lukacslacko/wonkycube/designs/pentagonal-prism-v1/plate-maps.html

# Wonky pentagonal prism — 60° — plate maps

Millimetres, 100% scale. Geometry only. Mark every piece with its full ID.

## C-01



## V-01



## H-01



## K-01



## V-face-down-01



## H-face-down-01



## K-radial-down-01



## core-01



## alternate-cores-01



## fit-coupons-01



## stand-01
