lukacslacko/wonkycube/designs/rhombic-dodecahedron-v5.1/NEIGHBORS.md

# Solved neighbors

T = threefold screwed center (8 copies), S = fourfold screwed center (6 copies), P = floating petal (24 copies). Every plastic copy within a type is identical; colored inlays identify the solved placement.

Each petal borders one T and one S center and straddles two rhombic faces. A T center has three neighboring petals; an S center has four. Neighbors here share an exterior seam; contact only at a tip is excluded.

| Piece | Seam neighbors |
|---|---|
| T01 | P01, P02, P03 |
| T02 | P04, P05, P06 |
| T03 | P07, P08, P09 |
| T04 | P10, P11, P12 |
| T05 | P13, P14, P15 |
| T06 | P16, P17, P18 |
| T07 | P19, P20, P21 |
| T08 | P22, P23, P24 |
| S01 | P01, P04, P07, P10 |
| S02 | P13, P16, P19, P22 |
| S03 | P02, P05, P14, P17 |
| S04 | P08, P11, P20, P23 |
| S05 | P03, P09, P15, P21 |
| S06 | P06, P12, P18, P24 |
| P01 | T01, S01 |
| P02 | T01, S03 |
| P03 | T01, S05 |
| P04 | T02, S01 |
| P05 | T02, S03 |
| P06 | T02, S06 |
| P07 | T03, S01 |
| P08 | T03, S04 |
| P09 | T03, S05 |
| P10 | T04, S01 |
| P11 | T04, S04 |
| P12 | T04, S06 |
| P13 | T05, S02 |
| P14 | T05, S03 |
| P15 | T05, S05 |
| P16 | T06, S02 |
| P17 | T06, S03 |
| P18 | T06, S06 |
| P19 | T07, S02 |
| P20 | T07, S04 |
| P21 | T07, S05 |
| P22 | T08, S02 |
| P23 | T08, S04 |
| P24 | T08, S06 |

## Axis labels

Coordinates use the six fourfold vertices as X/Y/Z. Threefold directions are listed as proportional vectors.

| Center | Direction | Ordinary turn |
|---|---|---|
| T01 | -1, -1, -1 | 120° |
| T02 | -1, -1, 1 | 120° |
| T03 | -1, 1, -1 | 120° |
| T04 | -1, 1, 1 | 120° |
| T05 | 1, -1, -1 | 120° |
| T06 | 1, -1, 1 | 120° |
| T07 | 1, 1, -1 | 120° |
| T08 | 1, 1, 1 | 120° |
| S01 | -1, 0, 0 | 90° |
| S02 | 1, 0, 0 | 90° |
| S03 | 0, -1, 0 | 90° |
| S04 | 0, 1, 0 | 90° |
| S05 | 0, 0, -1 | 90° |
| S06 | 0, 0, 1 | 90° |
