lukacslacko/wonkycube/designs/curvy-copter-cuboctahedron-v3.2/NEIGHBORS.md

# Solved neighbors

C = screwed center; P = petal; K = floating corner. Every copy in a family is identical. The plate names and painting map use these labels.

| Piece | Exterior seam neighbors |
|---|---|
| C01 | P01, P04, P05, P12 |
| C02 | P01, P02, P06, P07 |
| C03 | P02, P03, P08, P09 |
| C04 | P03, P04, P10, P11 |
| C05 | P05, P06, P13, P14 |
| C06 | P07, P08, P15, P16 |
| C07 | P09, P10, P17, P18 |
| C08 | P11, P12, P19, P20 |
| C09 | P13, P20, P21, P24 |
| C10 | P14, P15, P21, P22 |
| C11 | P16, P17, P22, P23 |
| C12 | P18, P19, P23, P24 |
| K01 | P01, P05, P06 |
| K02 | P02, P07, P08 |
| K03 | P03, P09, P10 |
| K04 | P04, P11, P12 |
| K05 | P13, P14, P21 |
| K06 | P15, P16, P22 |
| K07 | P17, P18, P23 |
| K08 | P19, P20, P24 |
| P01 | C01, C02, K01 |
| P02 | C02, C03, K02 |
| P03 | C03, C04, K03 |
| P04 | C01, C04, K04 |
| P05 | C01, C05, K01 |
| P06 | C02, C05, K01 |
| P07 | C02, C06, K02 |
| P08 | C03, C06, K02 |
| P09 | C03, C07, K03 |
| P10 | C04, C07, K03 |
| P11 | C04, C08, K04 |
| P12 | C01, C08, K04 |
| P13 | C05, C09, K05 |
| P14 | C05, C10, K05 |
| P15 | C06, C10, K06 |
| P16 | C06, C11, K06 |
| P17 | C07, C11, K07 |
| P18 | C07, C12, K07 |
| P19 | C08, C12, K08 |
| P20 | C08, C09, K08 |
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

| Center | Axis (proportional coordinates) |
|---|---|
| C01 | -1, 0, 1 |
| C02 | 0, -1, 1 |
| C03 | 1, 0, 1 |
| C04 | 0, 1, 1 |
| C05 | -1, -1, 0 |
| C06 | 1, -1, 0 |
| C07 | 1, 1, 0 |
| C08 | -1, 1, 0 |
| C09 | -1, 0, -1 |
| C10 | 0, -1, -1 |
| C11 | 1, 0, -1 |
| C12 | 0, 1, -1 |
