lukacslacko/wonkycube/designs/redi-v4.3/NEIGHBORS.md

# Solved neighbors — compact Redi v4.3

Use these **v4.2 Redi IDs**, not the 65° prototype’s edge ordering. Write each full ID on a sheltered inside patch, away from sliding surfaces. Tick each box after printing and marking.

Neighbors share an exterior seam in the solved state. Point contacts are excluded; the list is not clockwise. For orientation, use the named solved 3MF and the identification image. The core supports all eight C pieces.

| Marked | Piece | Solved seam neighbors |
|---|---|---|
| ☐ | C01 | E01, E02, E05 |
| ☐ | C02 | E01, E03, E06 |
| ☐ | C03 | E02, E04, E07 |
| ☐ | C04 | E03, E04, E08 |
| ☐ | C05 | E05, E09, E10 |
| ☐ | C06 | E06, E09, E11 |
| ☐ | C07 | E07, E10, E12 |
| ☐ | C08 | E08, E11, E12 |
| ☐ | E01 | C01, C02 |
| ☐ | E02 | C01, C03 |
| ☐ | E03 | C02, C04 |
| ☐ | E04 | C03, C04 |
| ☐ | E05 | C01, C05 |
| ☐ | E06 | C02, C06 |
| ☐ | E07 | C03, C07 |
| ☐ | E08 | C04, C08 |
| ☐ | E09 | C05, C06 |
| ☐ | E10 | C05, C07 |
| ☐ | E11 | C06, C08 |
| ☐ | E12 | C07, C08 |

For each E piece, its two C neighbors identify the two ends. Match the ends against the solved model before adding optional end labels. Assembly order is **E → C**; see [ASSEMBLY.md](ASSEMBLY.md).
