lukacslacko/wonkycube/designs/redi-v4.3/plate-maps.html

# Compact Redi v4.3 print plates

Edges point inward toward −Z, with their inner feet downward. These are geometry-only plates; choose slicer settings yourself.

## C-01



## E-01



## core-01



## fit-coupons-01



## optional-01



## optional-core-5.50-01



## optional-core-5.70-01
