lukacslacko/wonkycube/designs/conical-3x3-v1.1/images/catalog-E.png

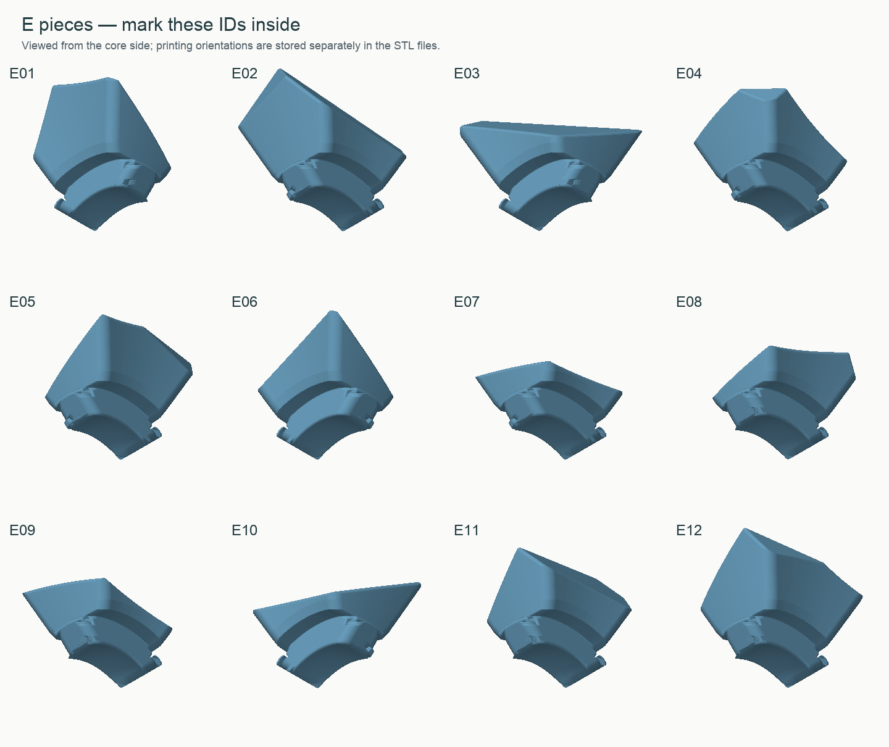
designs/conical-3x3-v1.1/images/catalog-E.png
