lukacslacko/wonkycube/designs/curvy-copter-cuboctahedron-v3.2/images/internal-pieces.png

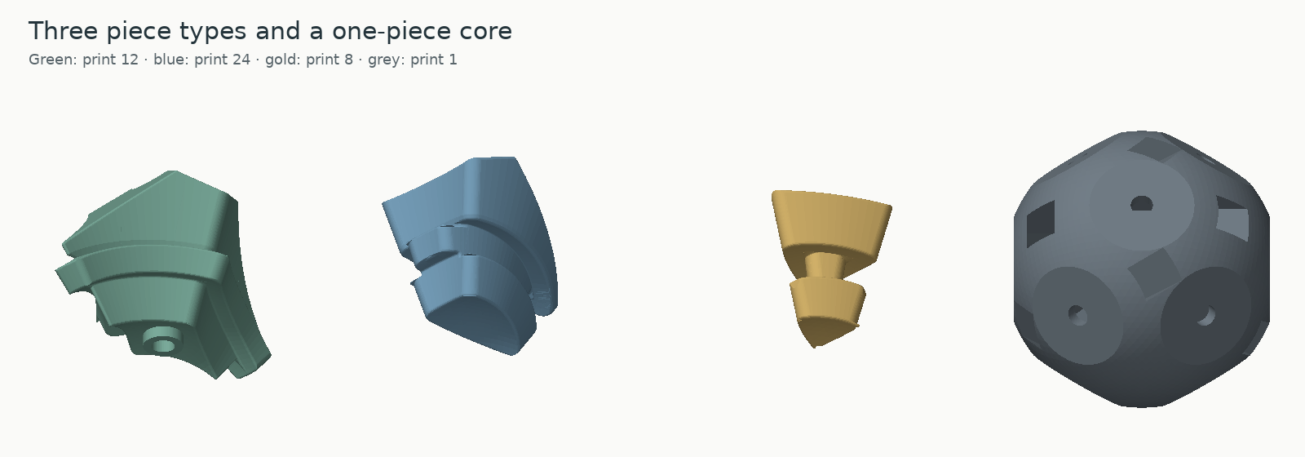
designs/curvy-copter-cuboctahedron-v3.2/images/internal-pieces.png
