lukacslacko/wonkycube/designs/curvy-copter-cuboctahedron-v3.2/images/spherical-profile.png

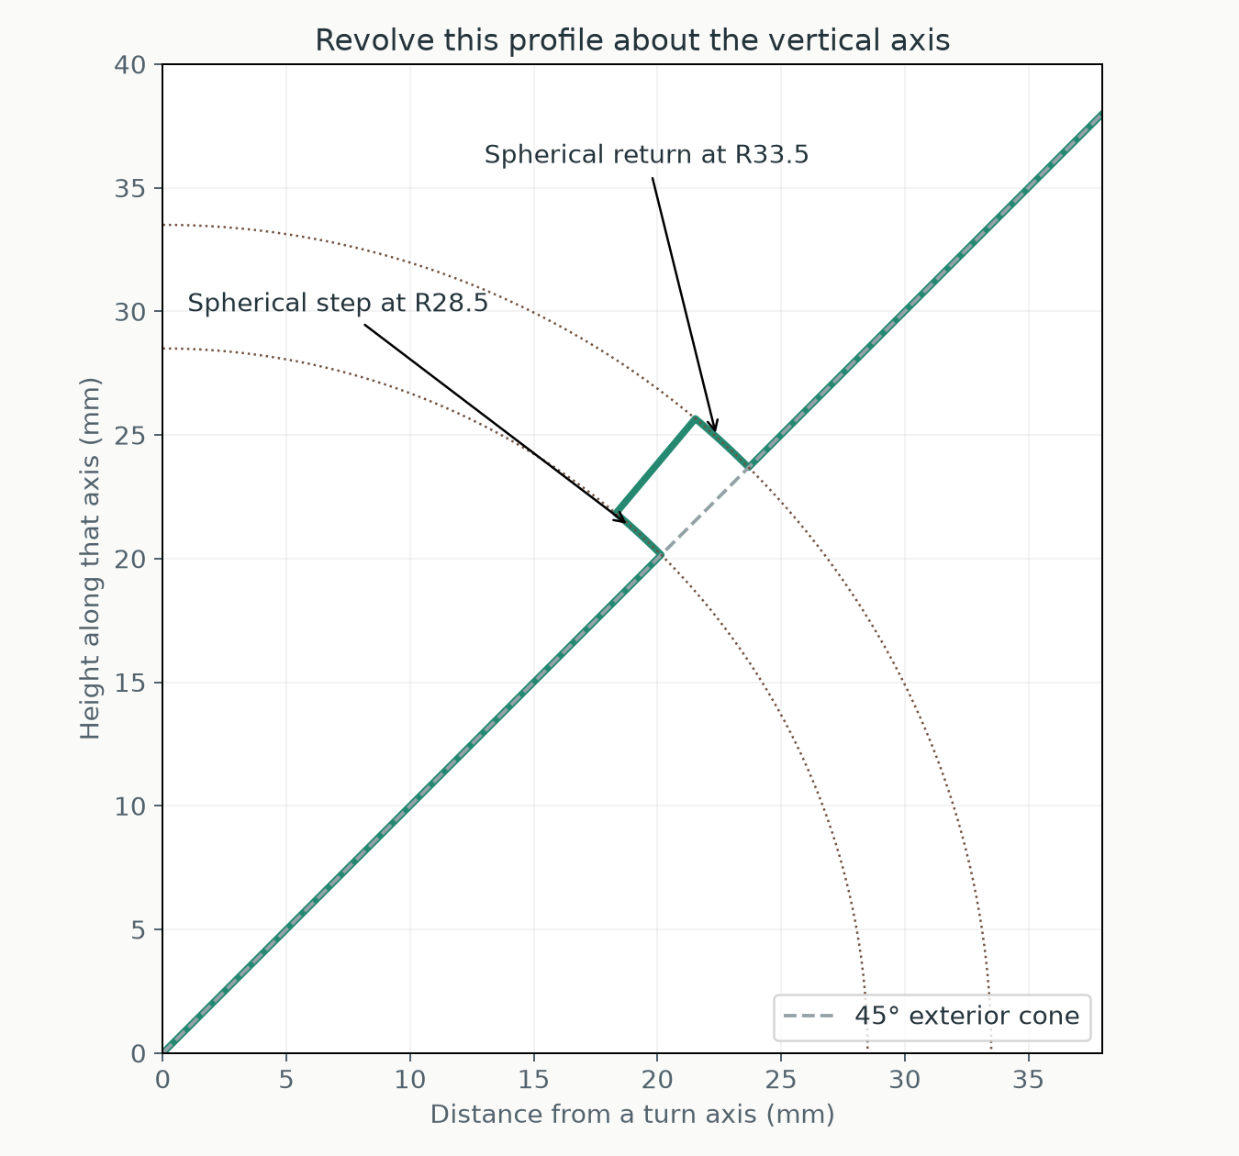
designs/curvy-copter-cuboctahedron-v3.2/images/spherical-profile.png
