lukacslacko/wonkycube/designs/redi-v4.3/images/piece-identification.png

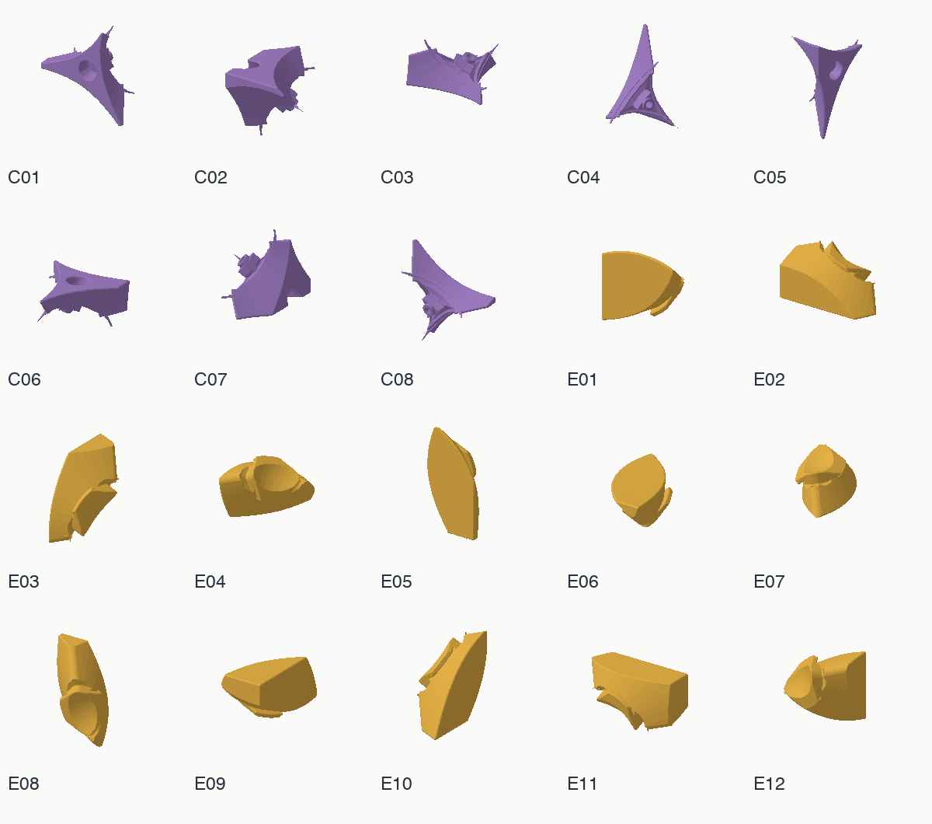
designs/redi-v4.3/images/piece-identification.png
