lukacslacko/wonkycube/designs/skewb-v1.1/images/core-identification.png

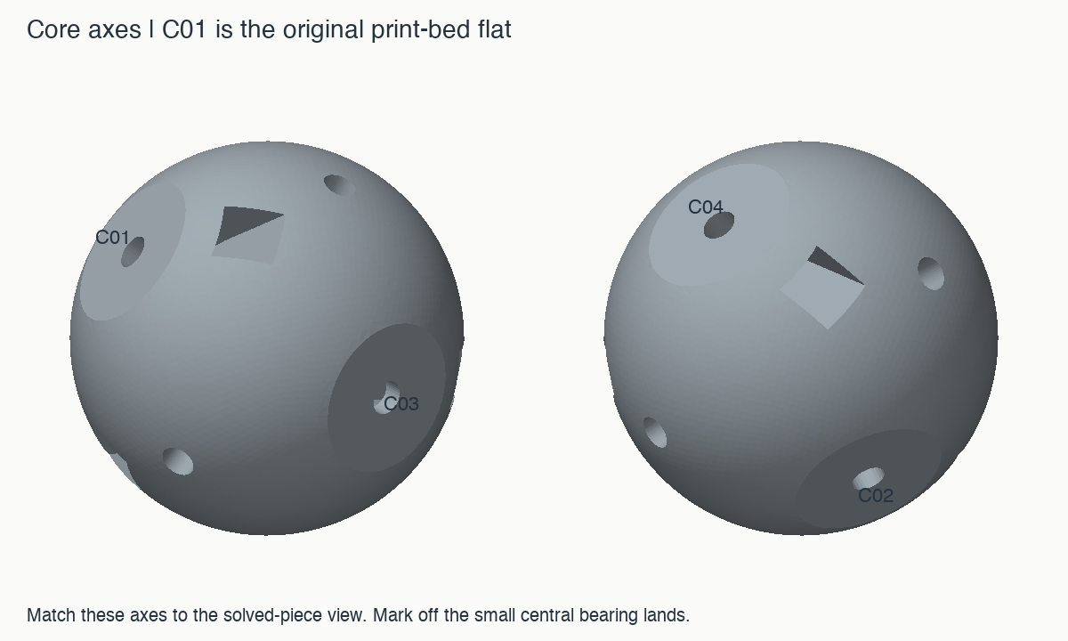
designs/skewb-v1.1/images/core-identification.png
