lukacslacko/wonkycube/designs/skewb-v1.1/images/mechanism.png

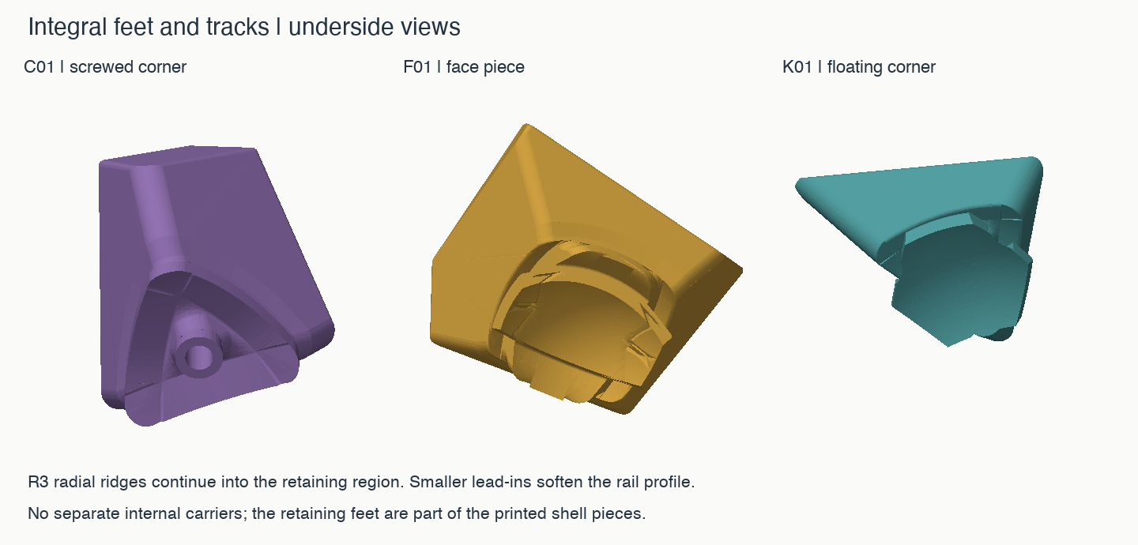
designs/skewb-v1.1/images/mechanism.png
