lukacslacko/wonkycube/designs/triangular-prism-v1/images/catalog-C.png

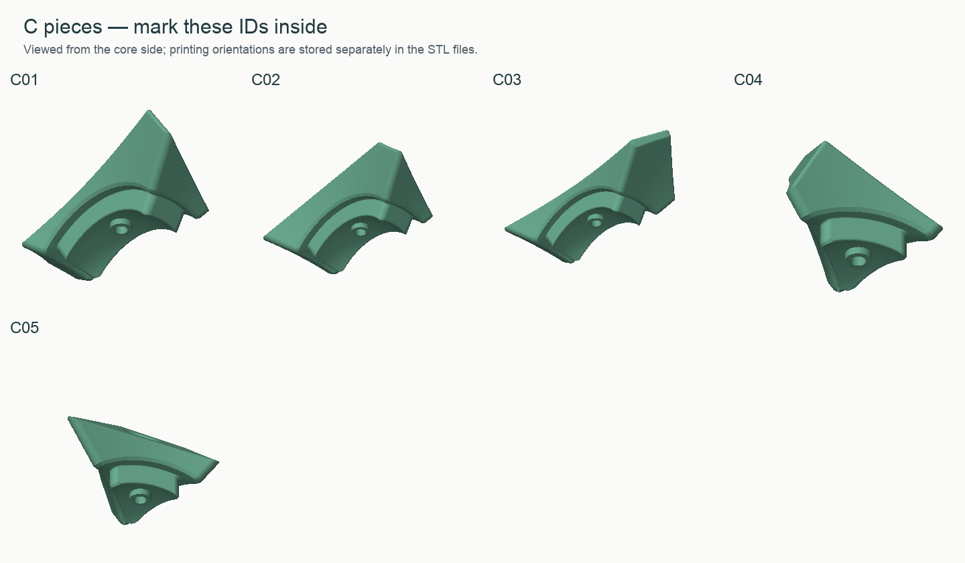
designs/triangular-prism-v1/images/catalog-C.png
