lukacslacko/wonkycube/designs/triangular-prism-v1/images/catalog-H.png

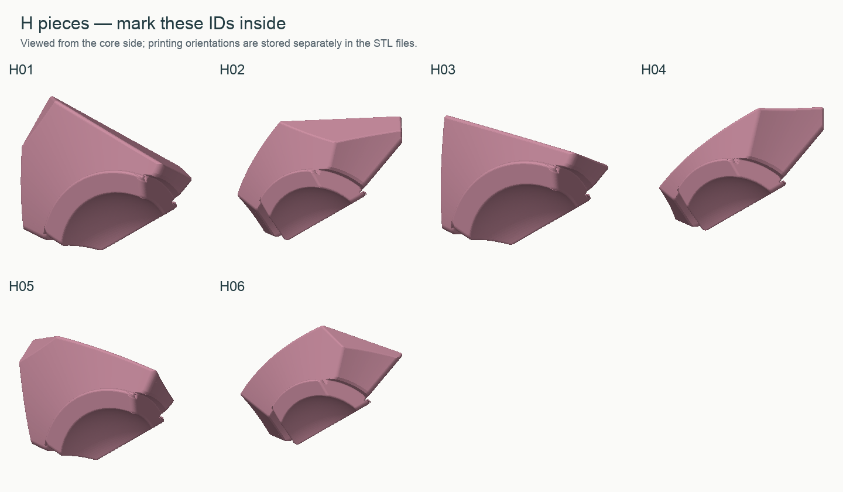
designs/triangular-prism-v1/images/catalog-H.png
