lukacslacko/wonkycube/designs/triangular-prism-v1/images/catalog-K.png

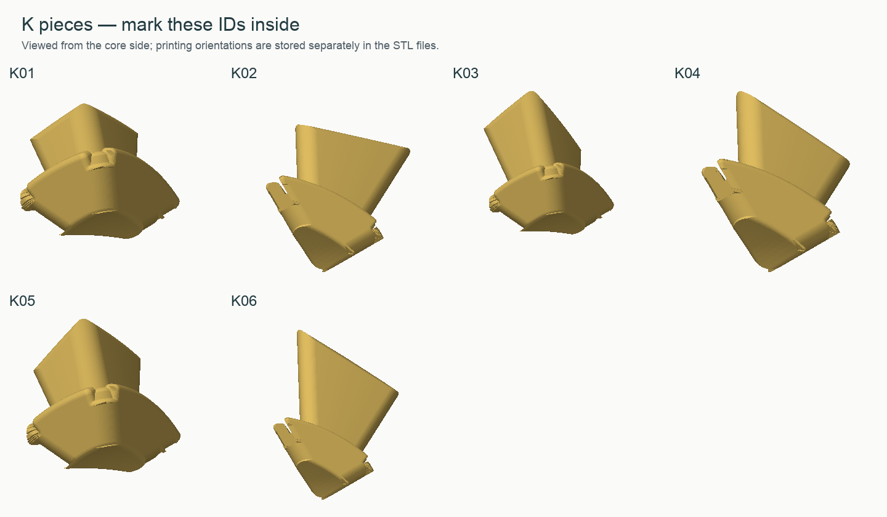
designs/triangular-prism-v1/images/catalog-K.png
