lukacslacko/wonkycube/designs/triangular-prism-v1/images/catalog-V.png

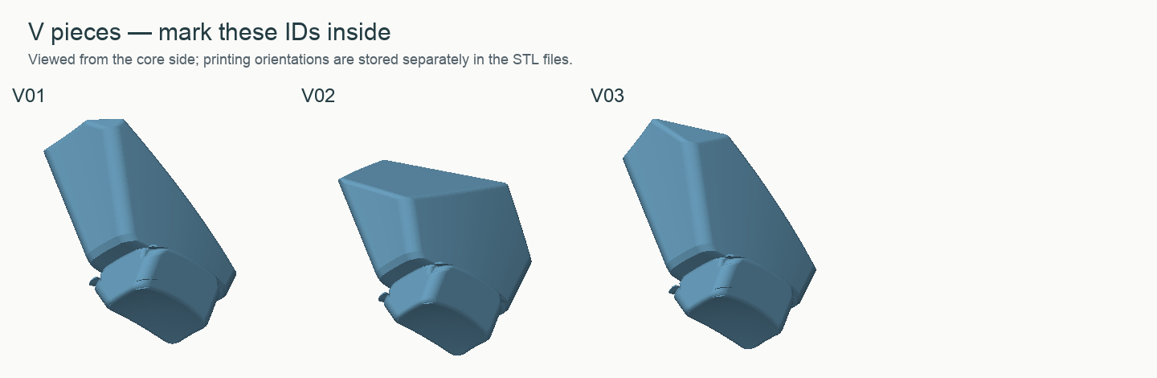
designs/triangular-prism-v1/images/catalog-V.png
