lukacslacko/wonkycube/designs/triangular-prism-v1/images/exploded.png

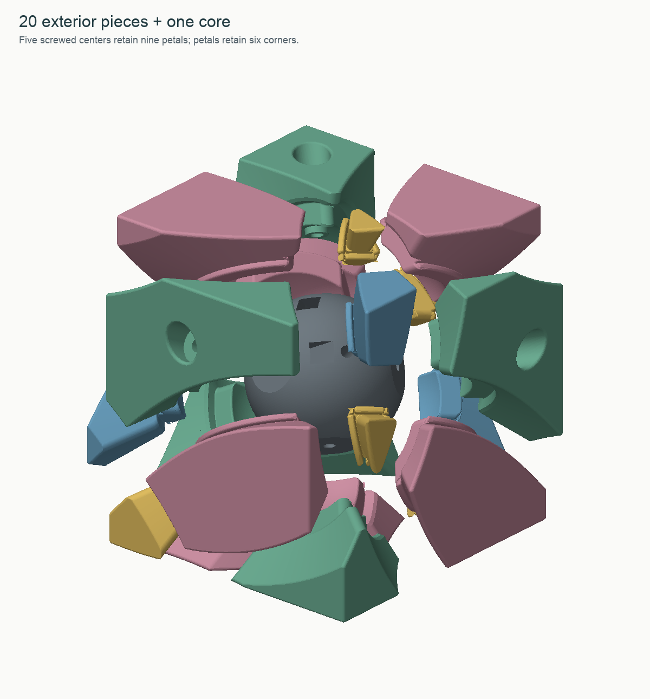
designs/triangular-prism-v1/images/exploded.png
