lukacslacko/wonkycube/designs/triangular-prism-v1/images/screw-stack-section.png

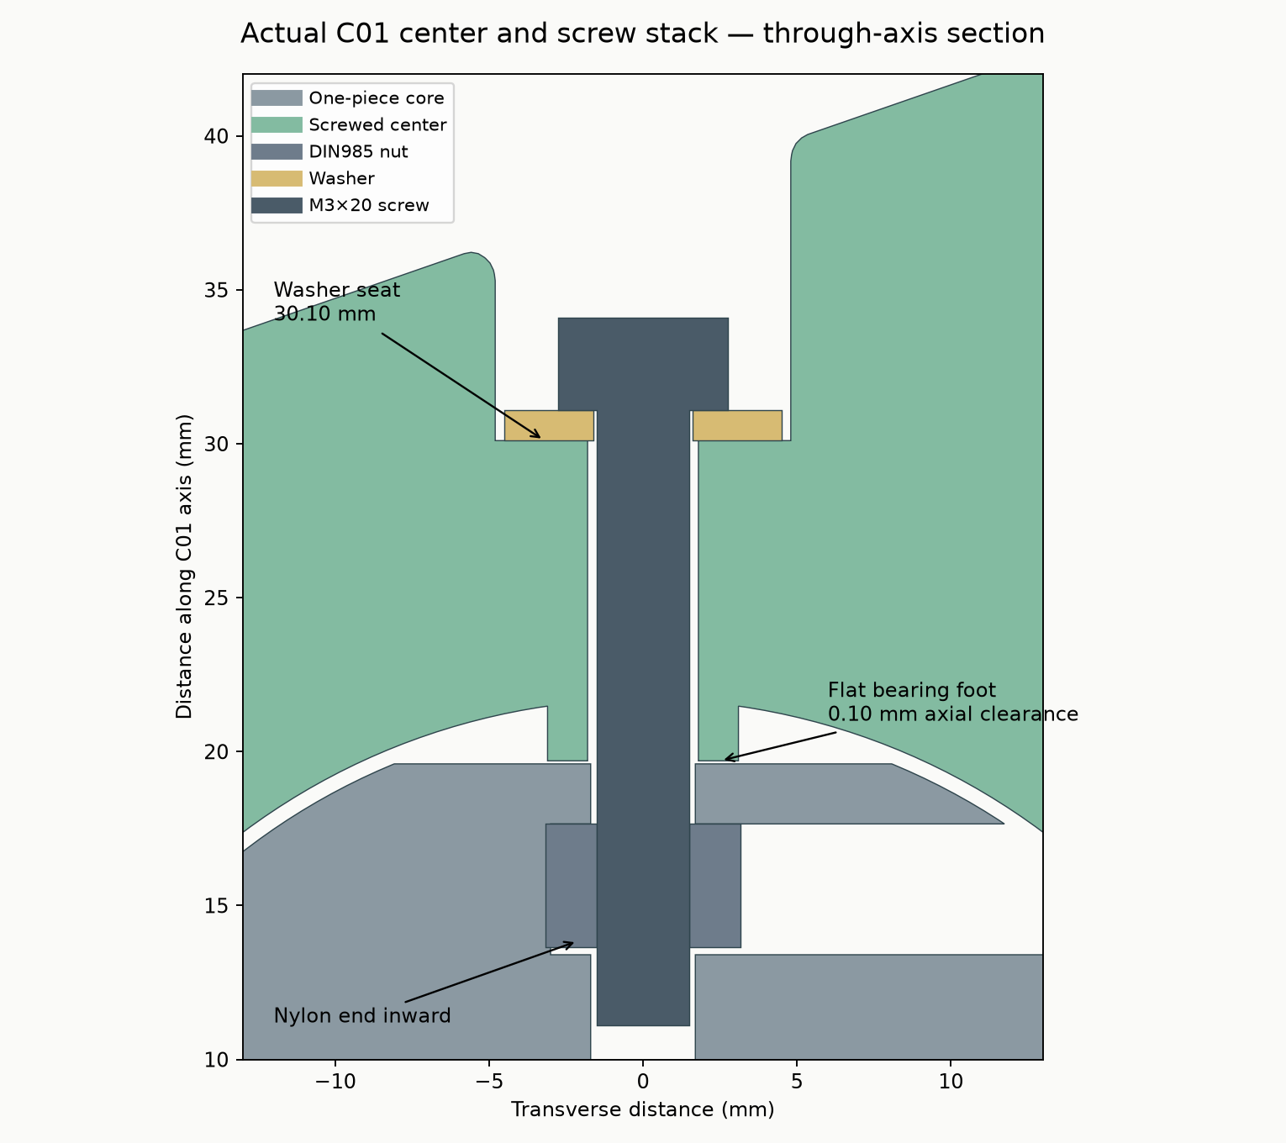
designs/triangular-prism-v1/images/screw-stack-section.png
