lukacslacko/wonkycube/designs/wavy-redi-v1.1/images/core.png

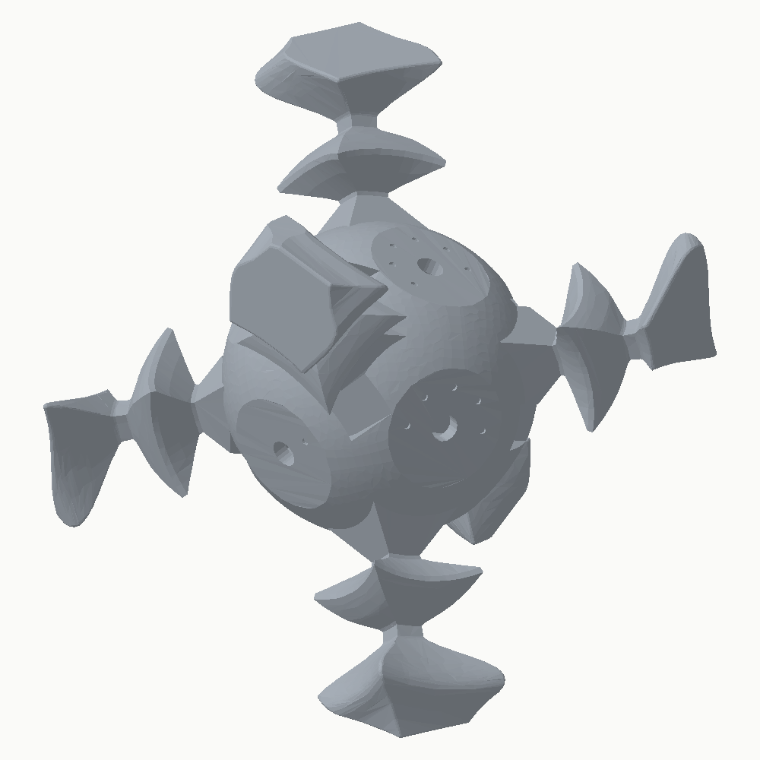
designs/wavy-redi-v1.1/images/core.png
