lukacslacko/wonkycube/docs/images/core-v3p1.png

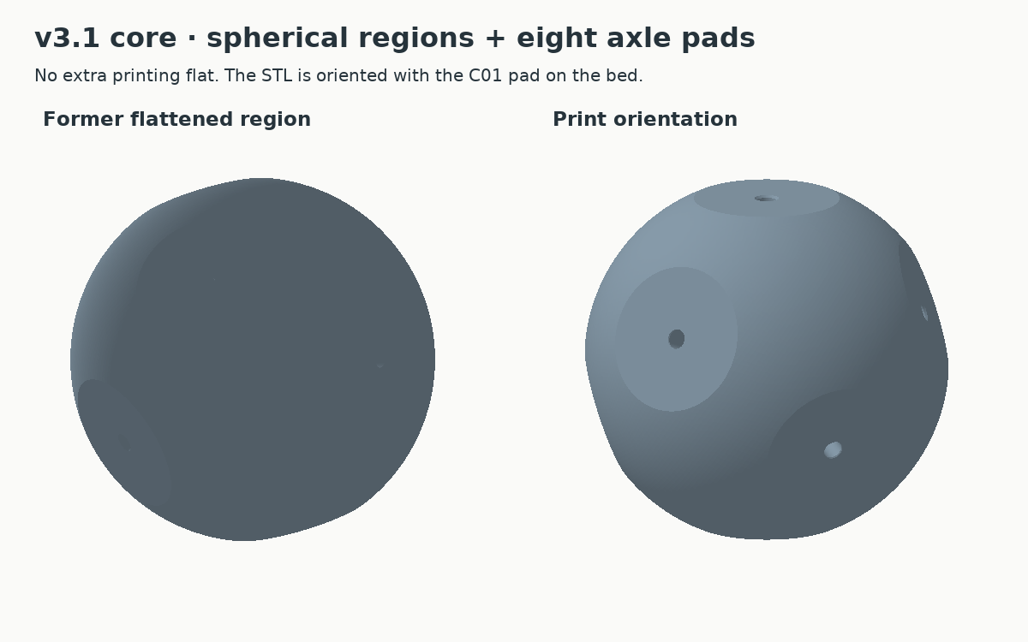
docs/images/core-v3p1.png
