lukacslacko/wonkycube/docs/images/five-cubes.png

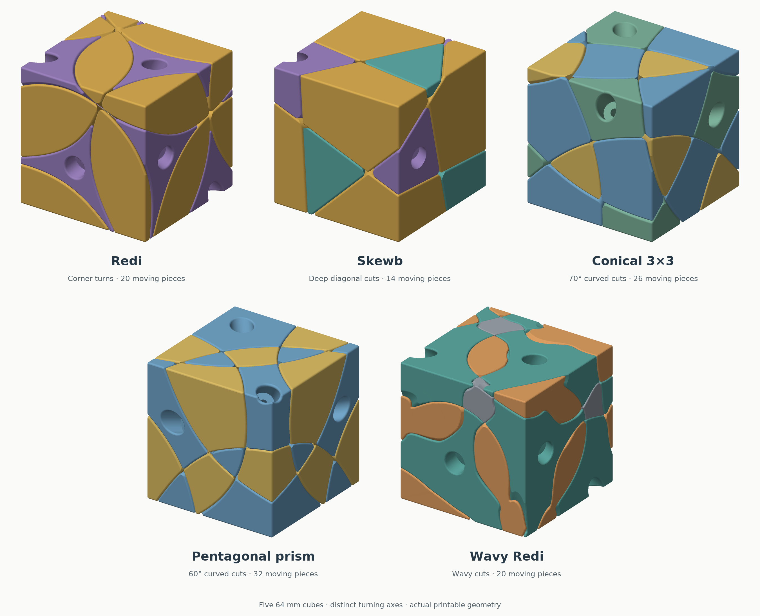
docs/images/five-cubes.png
