lukacslacko/wonkycube/docs/images/four-cubes.png

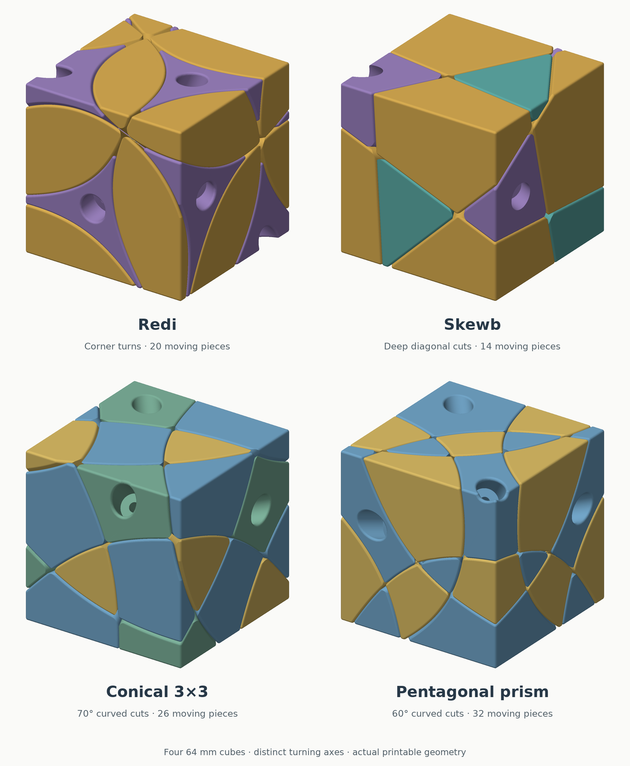
docs/images/four-cubes.png
