lukacslacko/wonkycube/docs/images/radial-ridges-v4p1.png

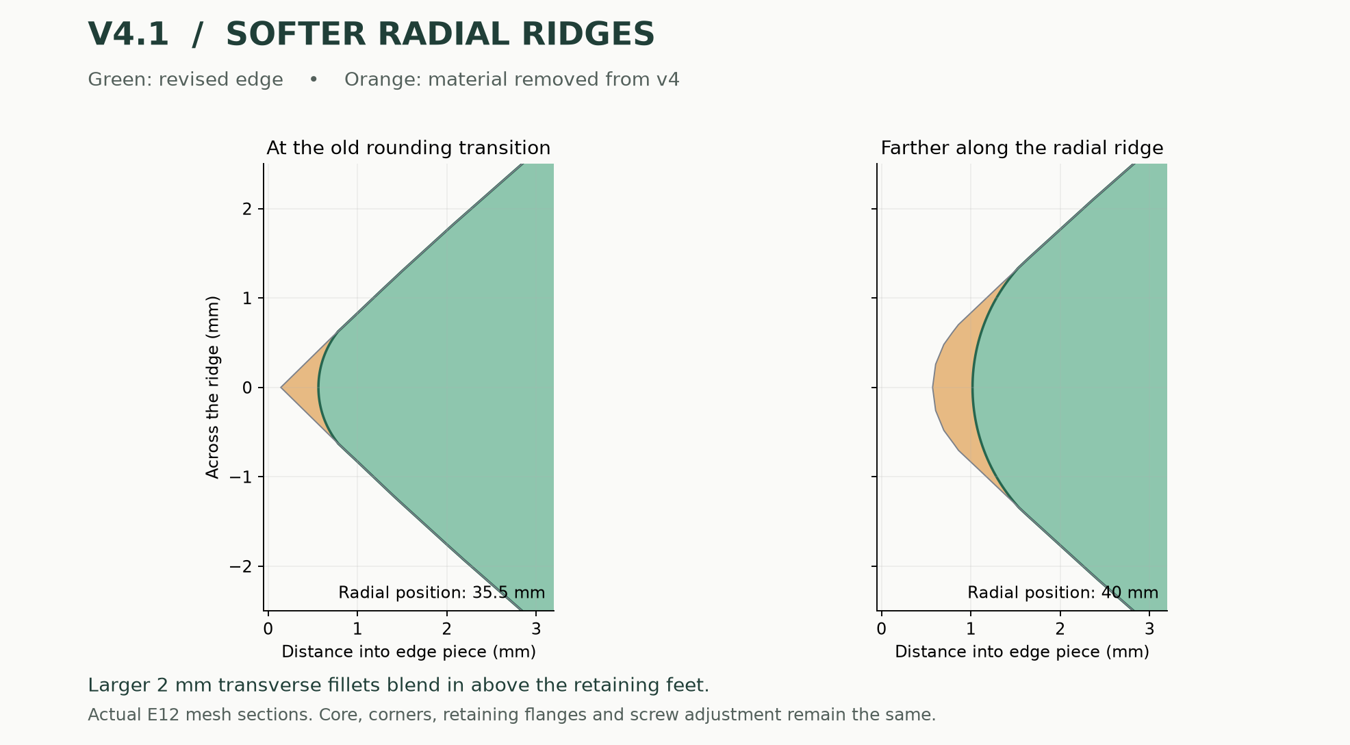
docs/images/radial-ridges-v4p1.png
