lukacslacko/wonkycube/docs/images/three-cubes.png

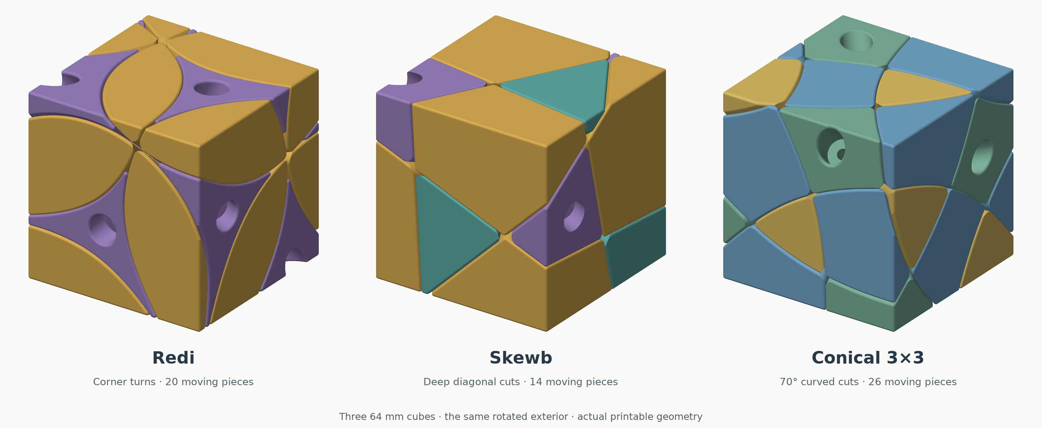
docs/images/three-cubes.png
