lukacslacko/wonkycube/docs/images/wonkycube.png

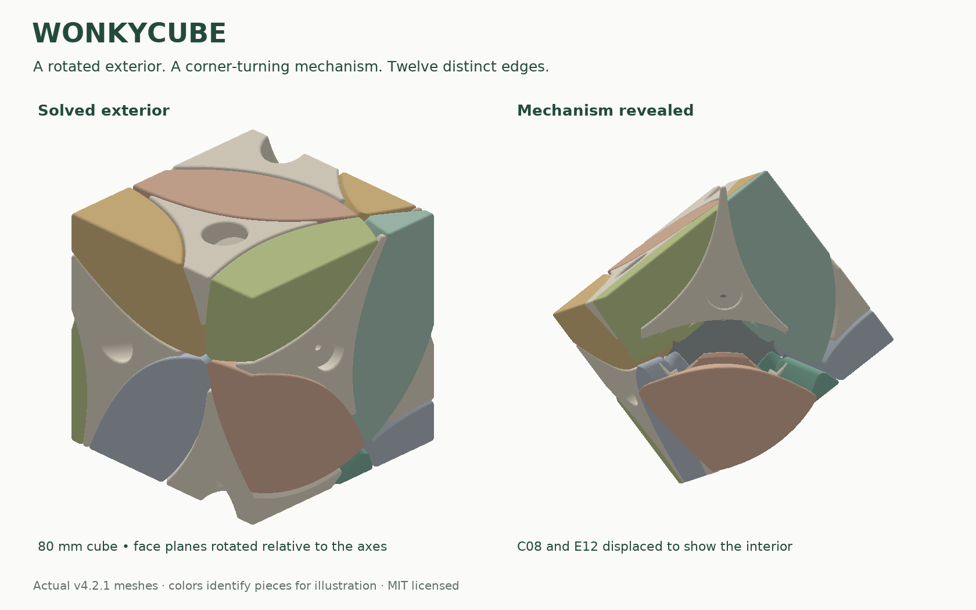
docs/images/wonkycube.png
