lukacslacko/wonkycube/models/current/reference/track-detail-v4p2.png

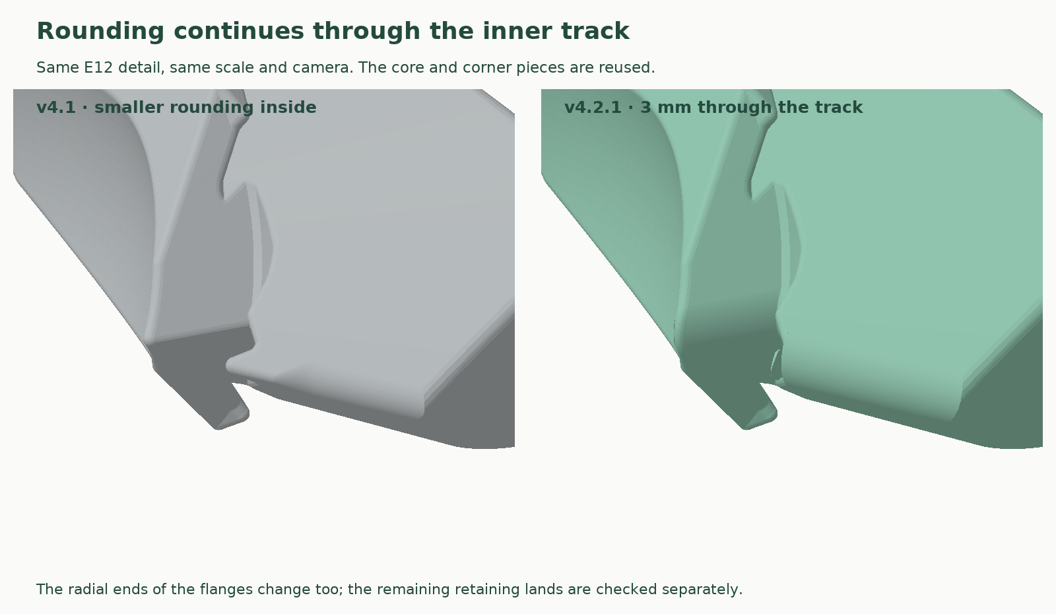
models/current/reference/track-detail-v4p2.png
