lukacslacko/wonkycube/designs/rhombic-dodecahedron-v5.1/images/parts.png

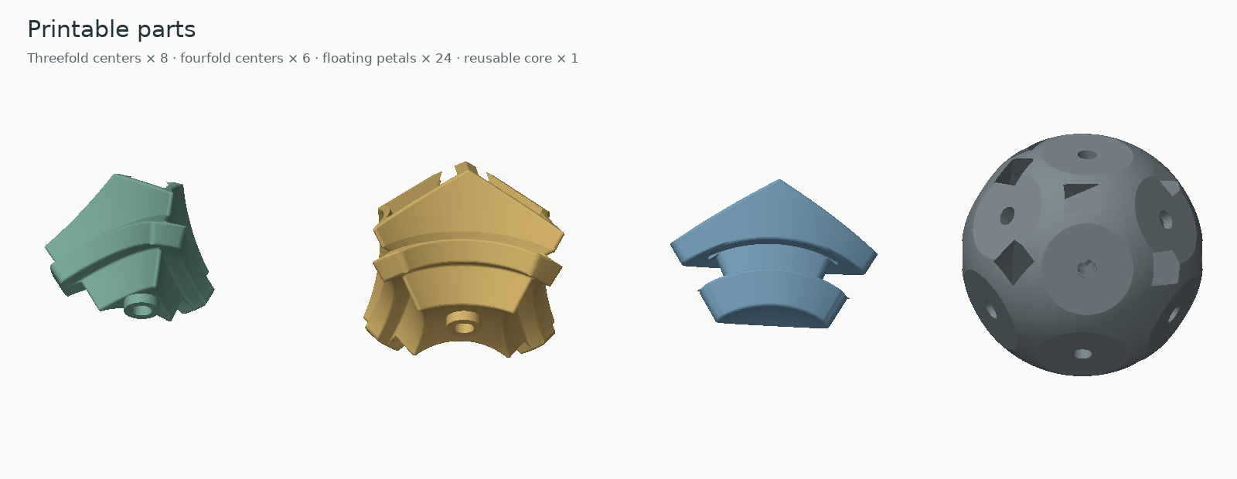
designs/rhombic-dodecahedron-v5.1/images/parts.png
