lukacslacko/wonkycube/designs/double-ivy-v7.1/plates/C-01.3mf

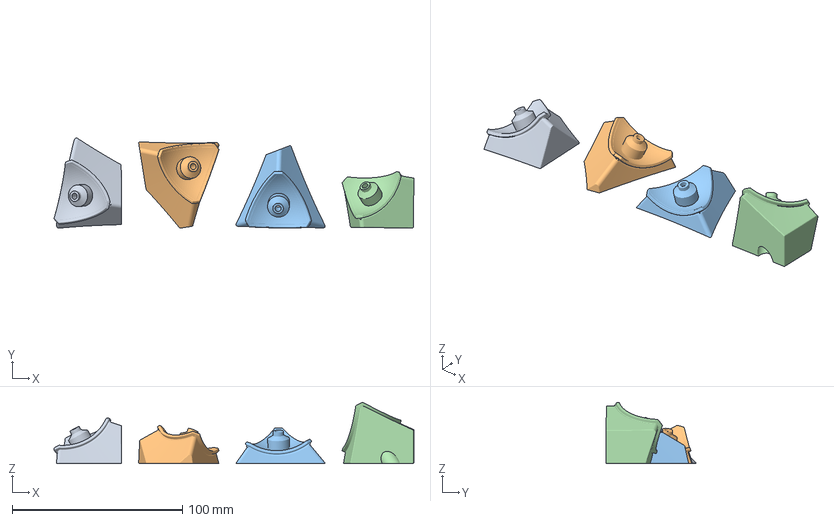
[picture p80: CAD file, 2026-09-30]
designs/double-ivy-v7.1/plates/C-01.3mf
211.6 x 53.1 x 35.9 mm
C03
C02
C04
C01
