lukacslacko/wonkycube/designs/double-ivy-v7.1/reference/DO-NOT-PRINT-solved.3mf

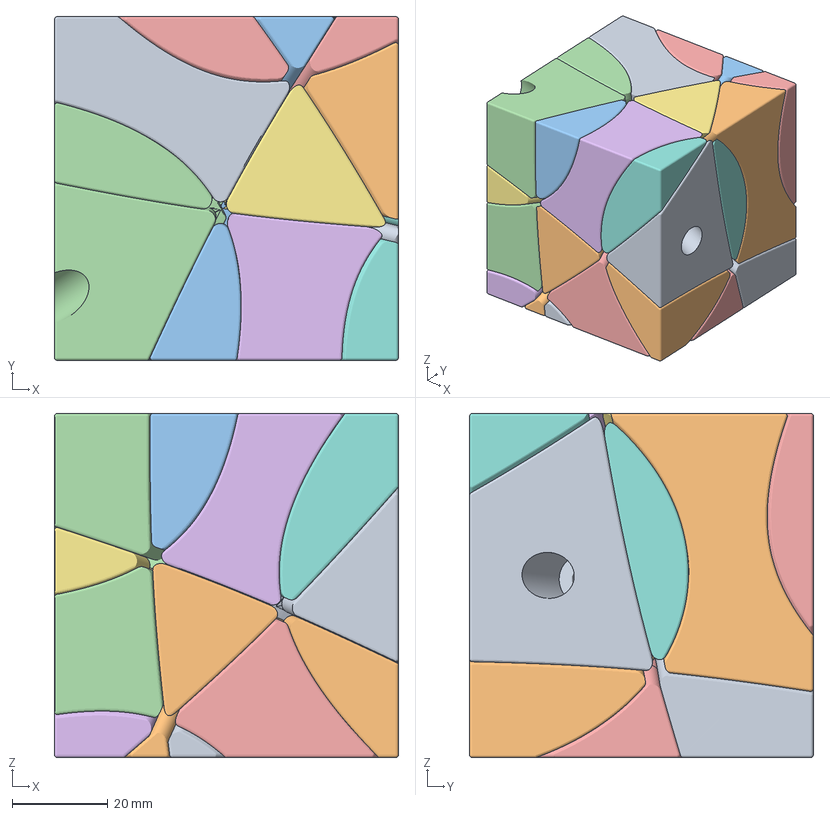
[picture p81: CAD file, 2026-09-30]
designs/double-ivy-v7.1/reference/DO-NOT-PRINT-solved.3mf
72.0 x 72.0 x 72.0 mm
C03
C02
C04
C01
W12
W04
W11
W07
W05
W08
W02
W03
W10
W06
W01
W09
E03
E06
E05
E01
E04
E02
F02
F03
F01
F04
core
