lukacslacko/wonkycube/designs/double-ivy-v7.1/reference/reused-core/core.stl

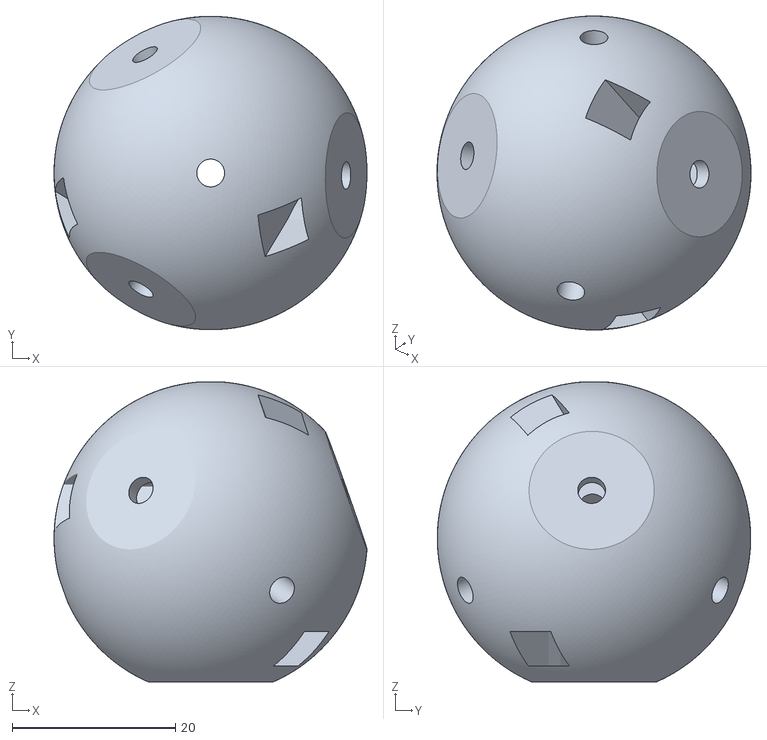
[picture p82: CAD file, 2026-09-18]
designs/double-ivy-v7.1/reference/reused-core/core.stl
38.3 x 38.4 x 36.7
