lukacslacko/wonkycube/designs/double-ivy-v7.1/stl/puzzle/W08.stl

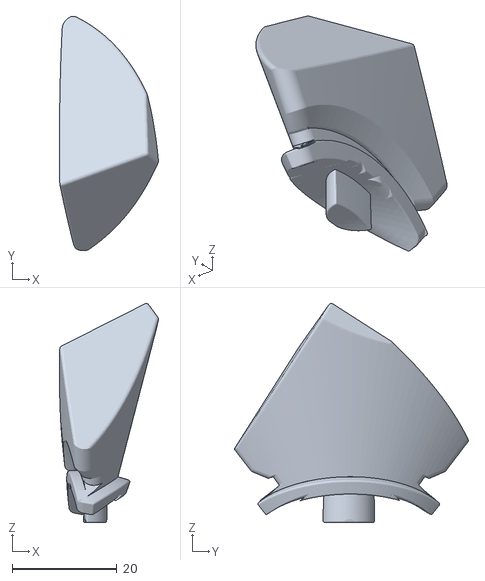
[picture p83: CAD file, 2026-09-30]
designs/double-ivy-v7.1/stl/puzzle/W08.stl
18.9 x 44.7 x 41.7
