lukacslacko/wonkycube/designs/face-turning-cuboctahedron-v1/stl/puzzle/triangle-center-print-8.stl

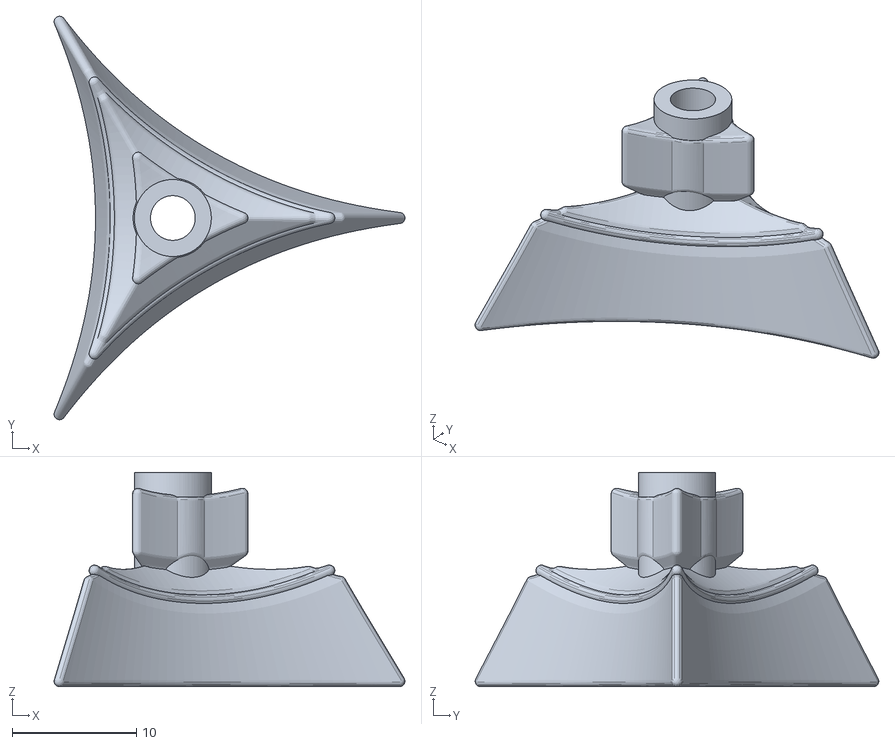
[picture p84: CAD file, 2026-09-28]
designs/face-turning-cuboctahedron-v1/stl/puzzle/triangle-center-print-8.stl
28.3 x 32.5 x 17.3
