lukacslacko/wonkycube/designs/pentagonal-prism-v1/plates/V-01.3mf

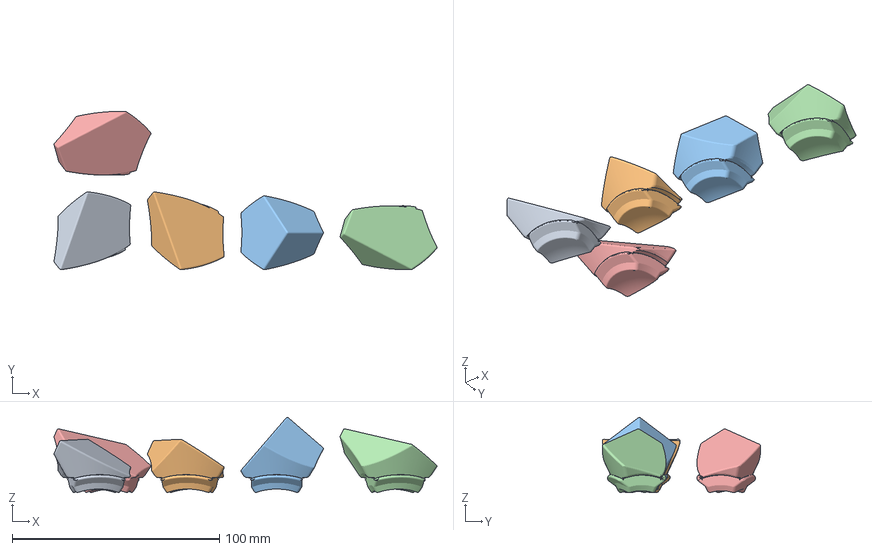
[picture p85: CAD file, 2026-09-23]
designs/pentagonal-prism-v1/plates/V-01.3mf
184.8 x 76.5 x 36.3 mm
V05
V02
V03
V04
V01
