lukacslacko/wonkycube/designs/pentagonal-prism-v1/print-options/H06-face-down.3mf

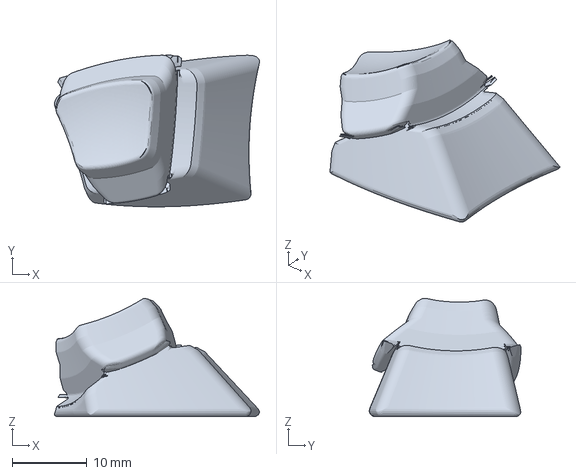
[picture p86: CAD file, 2026-09-23]
designs/pentagonal-prism-v1/print-options/H06-face-down.3mf
27.3 x 20.2 x 15.8 mm
