lukacslacko/wonkycube/designs/pentagonal-prism-v1/stl/puzzle/H08.stl

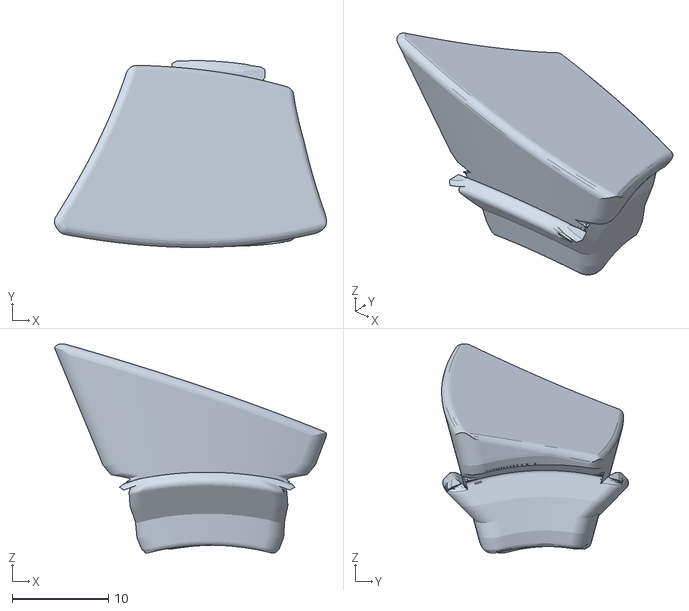
[picture p87: CAD file, 2026-09-23]
designs/pentagonal-prism-v1/stl/puzzle/H08.stl
28.2 x 19.4 x 21.7
