lukacslacko/wonkycube/designs/redi-v4.3/plates/E-01.3mf

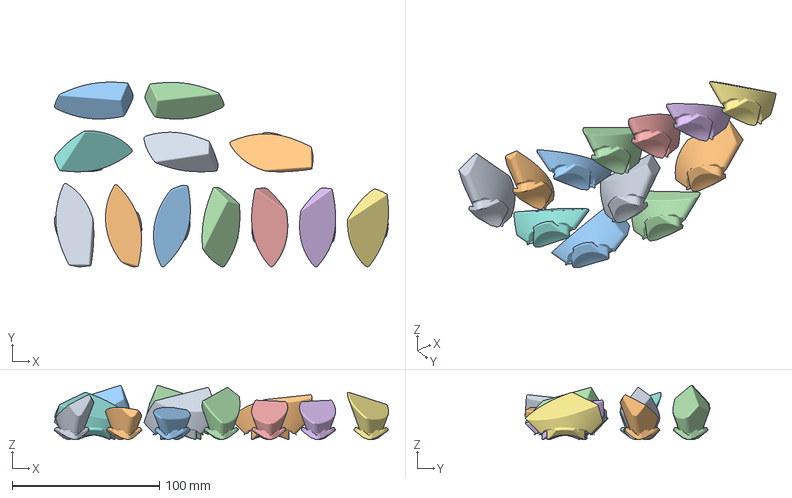
[picture p88: CAD file, 2026-09-17]
designs/redi-v4.3/plates/E-01.3mf
227.1 x 125.6 x 36.9 mm
E05
E06
E07
E04
E03
E10
E12
E01
E09
E08
E11
E02
