lukacslacko/wonkycube/designs/redi-v4.3/stl/fit-coupons/rotor-fit.stl

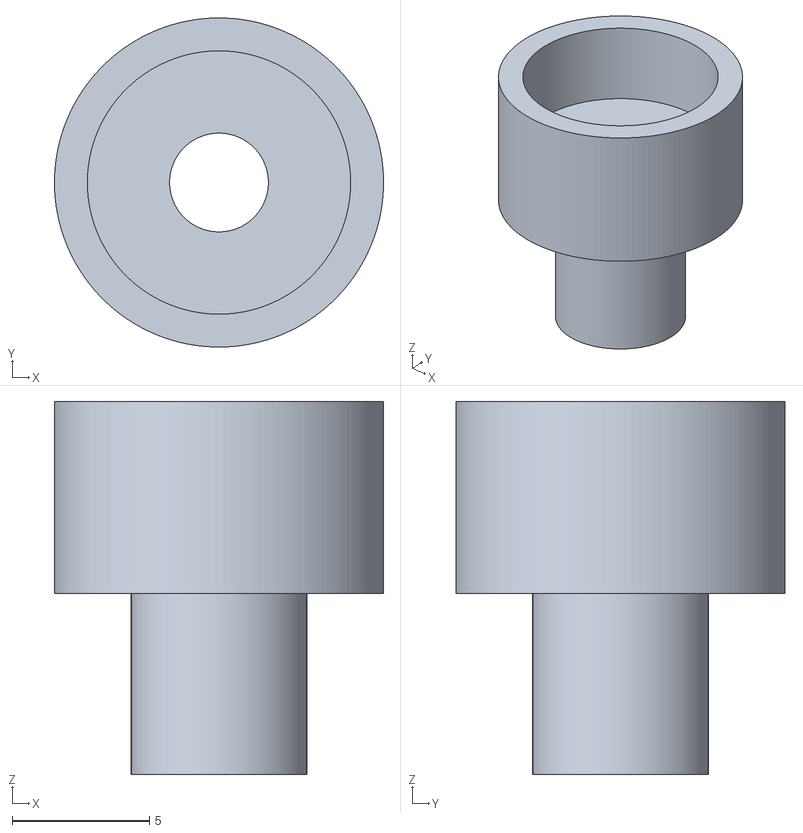
[picture p89: CAD file, 2026-09-17]
designs/redi-v4.3/stl/fit-coupons/rotor-fit.stl
12.0 x 12.0 x 13.6
