lukacslacko/wonkycube/designs/rhombic-dodecahedron-v5.1/inlays/fit-test/calibration-20mm.dxf

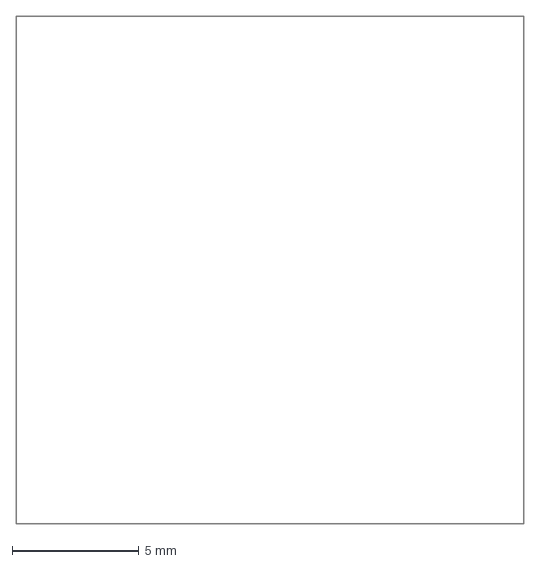
[picture p90: CAD file, 2026-10-06]
designs/rhombic-dodecahedron-v5.1/inlays/fit-test/calibration-20mm.dxf
20.0 x 20.0 mm
