lukacslacko/wonkycube/designs/rhombic-dodecahedron-v5.1/inlays/fit-variants/easy/easy-F07.dxf

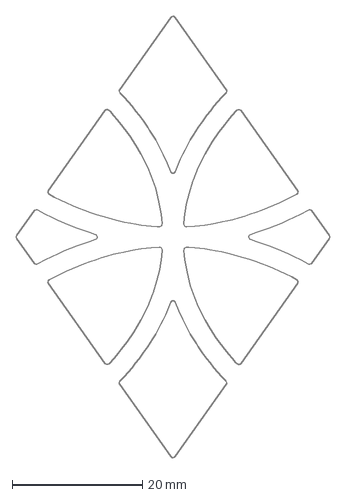
[picture p91: CAD file, 2026-10-06]
designs/rhombic-dodecahedron-v5.1/inlays/fit-variants/easy/easy-F07.dxf
48.2 x 67.9 mm
