lukacslacko/wonkycube/designs/rhombic-dodecahedron-v5.1/inlays/printable/faces/F12.3mf

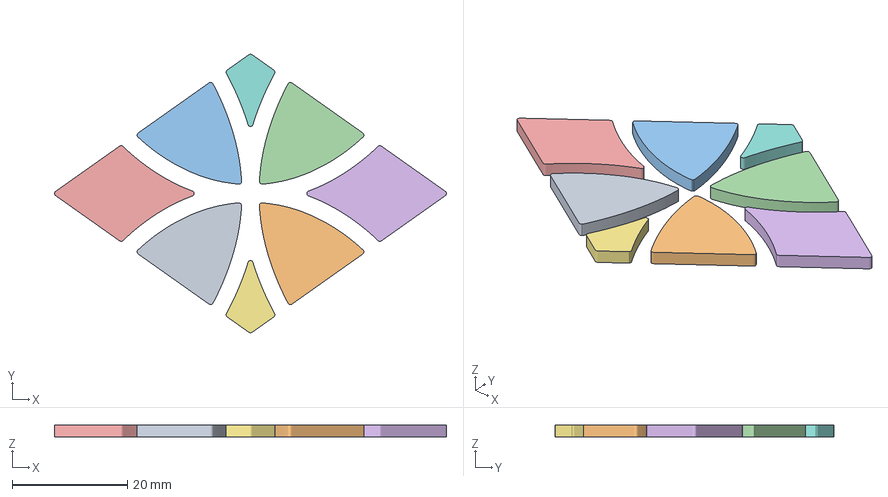
[picture p93: CAD file, 2026-10-06]
designs/rhombic-dodecahedron-v5.1/inlays/printable/faces/F12.3mf
67.9 x 48.3 x 2.00 mm
F12-P19
F12-P20
F12-P22
F12-P23
F12-S02
F12-S04
F12-T07
F12-T08
