lukacslacko/wonkycube/designs/rhombic-dodecahedron-v5.1/inlays/printable/individual/F01/F01-T05.stl

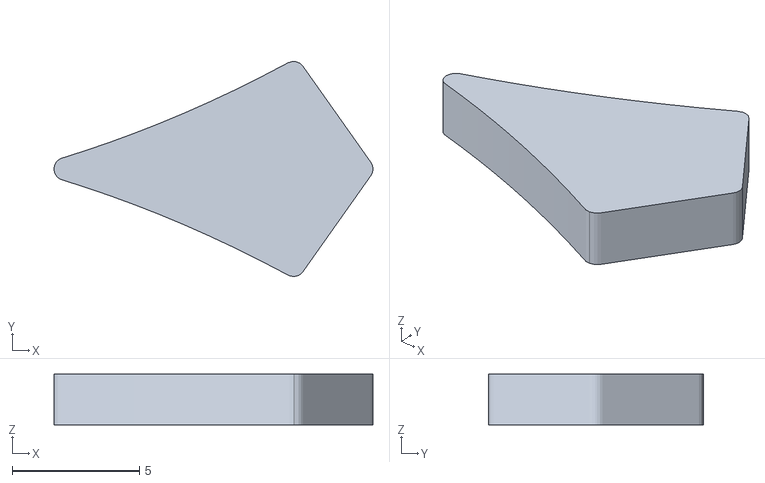
[picture p94: CAD file, 2026-10-06]
designs/rhombic-dodecahedron-v5.1/inlays/printable/individual/F01/F01-T05.stl
12.5 x 8.46 x 2.00
