lukacslacko/wonkycube/designs/rhombic-dodecahedron-v5.1/inlays/printable/individual/F02/F02-S03.stl

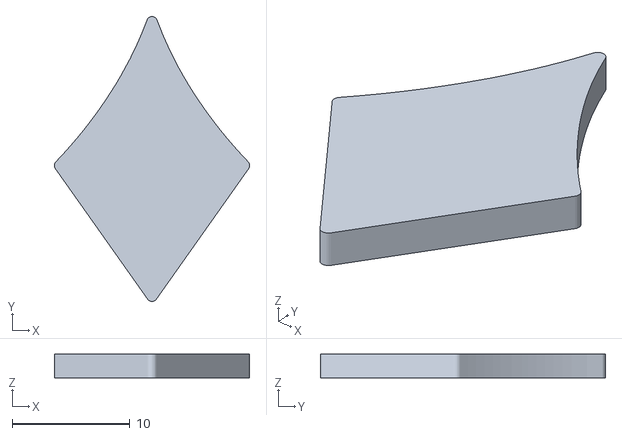
[picture p95: CAD file, 2026-10-06]
designs/rhombic-dodecahedron-v5.1/inlays/printable/individual/F02/F02-S03.stl
16.6 x 24.2 x 2.00
