lukacslacko/wonkycube/designs/rhombic-dodecahedron-v5.1/inlays/printable/individual/F03/F03-P08.stl

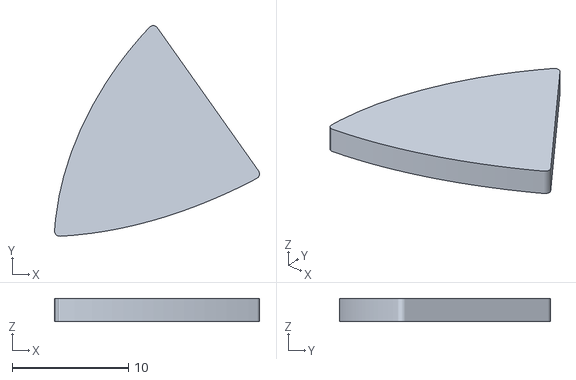
[picture p96: CAD file, 2026-10-06]
designs/rhombic-dodecahedron-v5.1/inlays/printable/individual/F03/F03-P08.stl
17.6 x 18.1 x 2.00
