lukacslacko/wonkycube/designs/rhombic-dodecahedron-v5.1/plates/caps-01.3mf

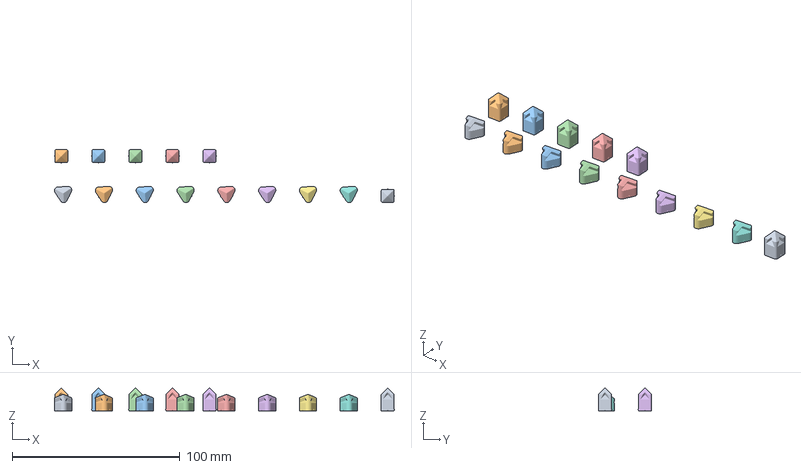
[picture p97: CAD file, 2026-10-06]
designs/rhombic-dodecahedron-v5.1/plates/caps-01.3mf
202.5 x 31.8 x 13.6 mm
T01-cap
T02-cap
T03-cap
T04-cap
T05-cap
T06-cap
T07-cap
T08-cap
S01-cap
S02-cap
S03-cap
S04-cap
S05-cap
S06-cap
