lukacslacko/wonkycube/designs/rhombic-dodecahedron-v5.1/stl/fit-coupons/fourfold-key-peg.stl

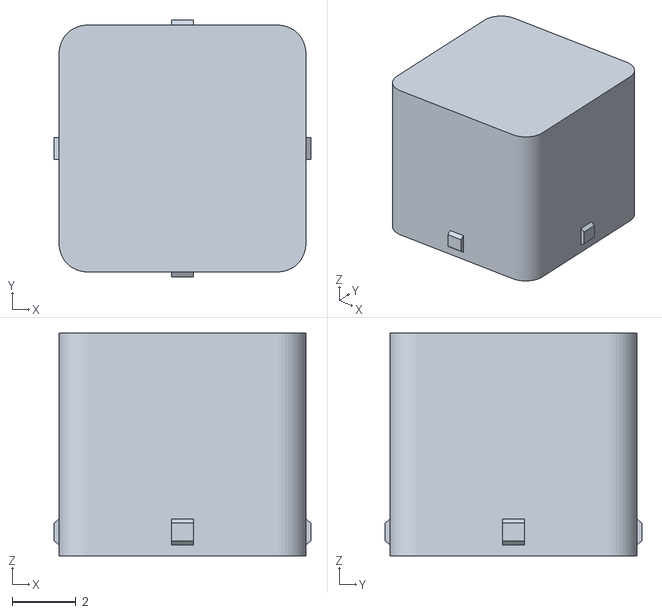
[picture p99: CAD file, 2026-10-06]
designs/rhombic-dodecahedron-v5.1/stl/fit-coupons/fourfold-key-peg.stl
8.08 x 8.08 x 7.00
