lukacslacko/wonkycube/designs/rhombic-dodecahedron-v5.1/stl/puzzle/fourfold-center-print-6.stl

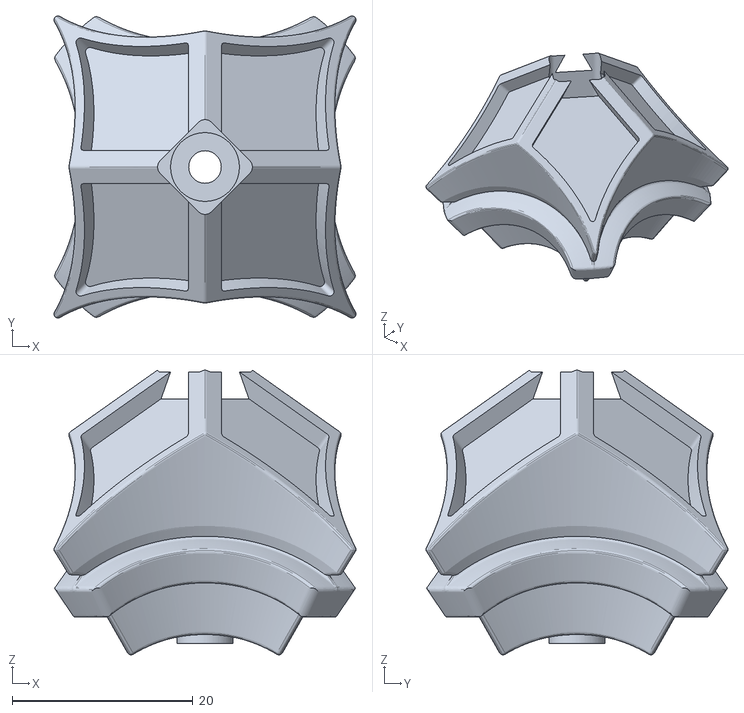
[picture p100: CAD file, 2026-10-06]
designs/rhombic-dodecahedron-v5.1/stl/puzzle/fourfold-center-print-6.stl
33.4 x 33.4 x 31.5
