lukacslacko/wonkycube/designs/skewb-v1.1/plates/alternate-cores-01.3mf

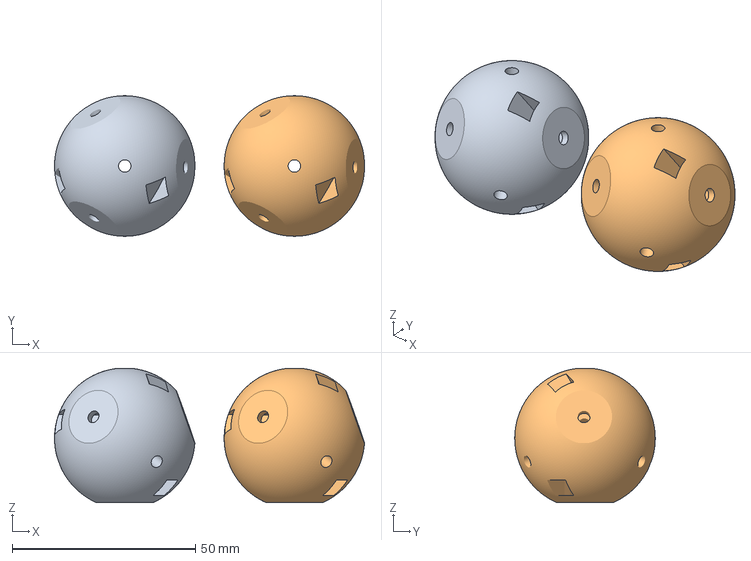
[picture p101: CAD file, 2026-09-18]
designs/skewb-v1.1/plates/alternate-cores-01.3mf
84.7 x 38.4 x 36.7 mm
core-seat-5.30
core-seat-5.50
