lukacslacko/wonkycube/designs/skewb-v1.1/print-options/F04-face-down.3mf

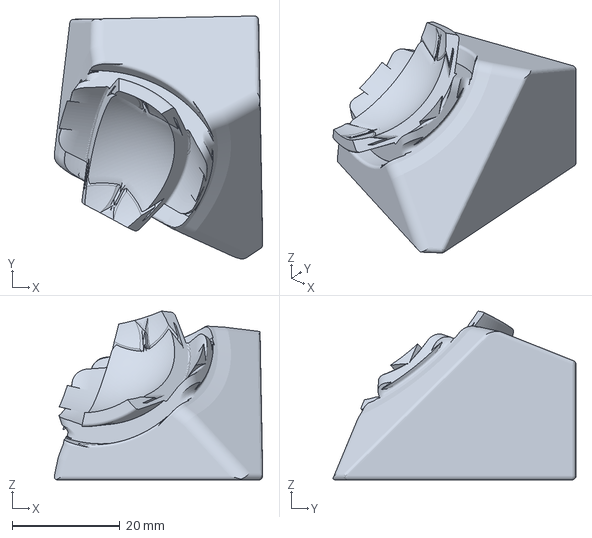
[picture p102: CAD file, 2026-09-18]
designs/skewb-v1.1/print-options/F04-face-down.3mf
38.6 x 45.0 x 31.3 mm
