lukacslacko/wonkycube/designs/skewb-v1.1/stl/puzzle/F03.stl

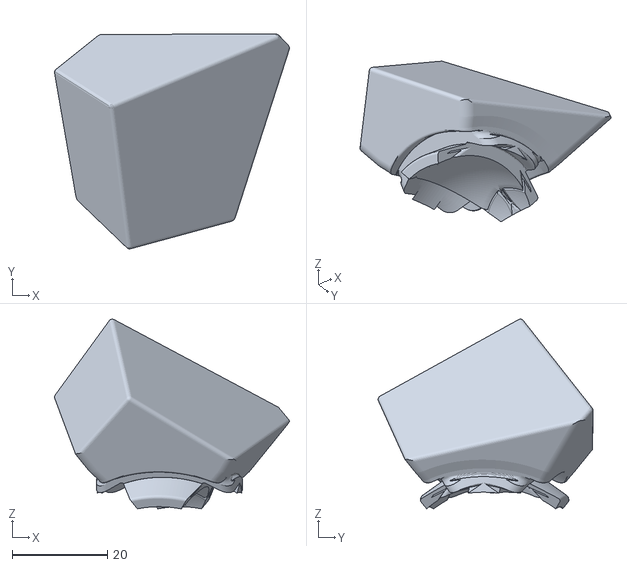
[picture p103: CAD file, 2026-09-18]
designs/skewb-v1.1/stl/puzzle/F03.stl
49.3 x 45.1 x 39.9
