lukacslacko/wonkycube/designs/triangular-prism-v1/plates/alternate-cores-01.3mf

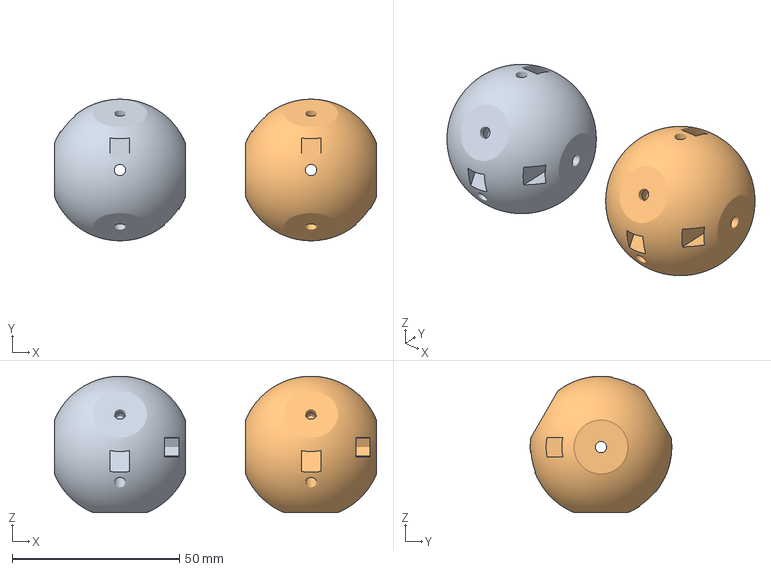
[picture p104: CAD file, 2026-09-27]
designs/triangular-prism-v1/plates/alternate-cores-01.3mf
96.4 x 42.4 x 40.7 mm
core-seat-5.30
core-seat-5.40
