lukacslacko/wonkycube/designs/triangular-prism-v1/reference/DO-NOT-PRINT-solved.3mf

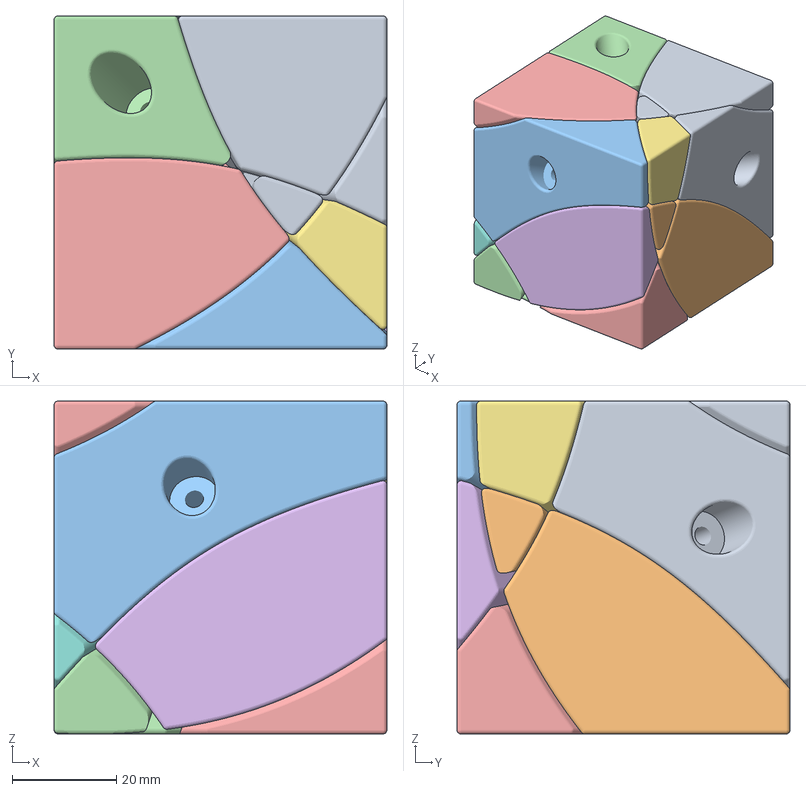
[picture p105: CAD file, 2026-09-27]
designs/triangular-prism-v1/reference/DO-NOT-PRINT-solved.3mf
64.0 x 64.0 x 64.0 mm
C01
C02
C03
C04
C05
V01
V02
V03
H01
H02
H03
H04
H05
H06
K01
K02
K03
K04
K05
K06
core
