lukacslacko/wonkycube/designs/triangular-prism-v1/stl/fit-coupons/rotor-fit.stl

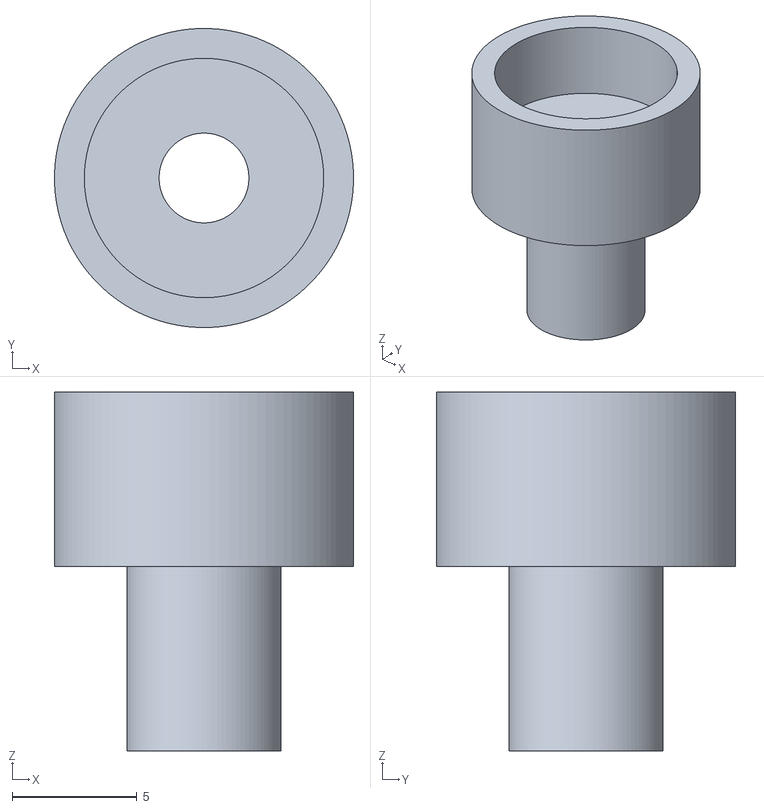
[picture p106: CAD file, 2026-09-27]
designs/triangular-prism-v1/stl/fit-coupons/rotor-fit.stl
12.0 x 12.0 x 14.4
