lukacslacko/wonkycube/designs/triangular-prism-v1/stl/optional/core-seat-5.40.stl

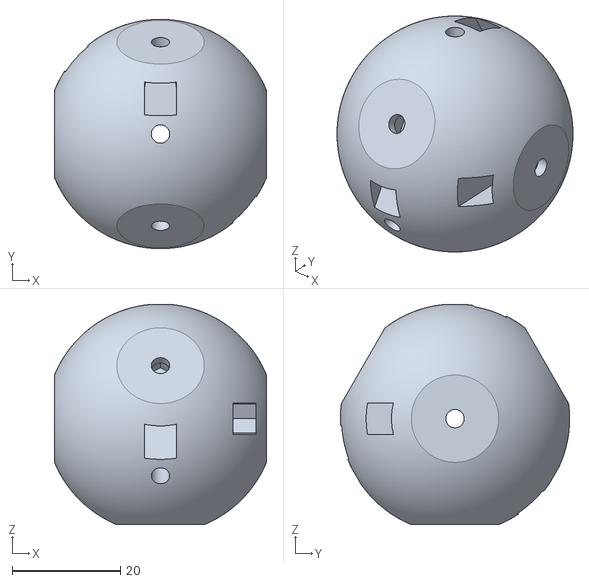
[picture p107: CAD file, 2026-09-27]
designs/triangular-prism-v1/stl/optional/core-seat-5.40.stl
39.2 x 42.4 x 40.7
