lukacslacko/wonkycube/designs/triangular-prism-v1/stl/puzzle/H01.stl

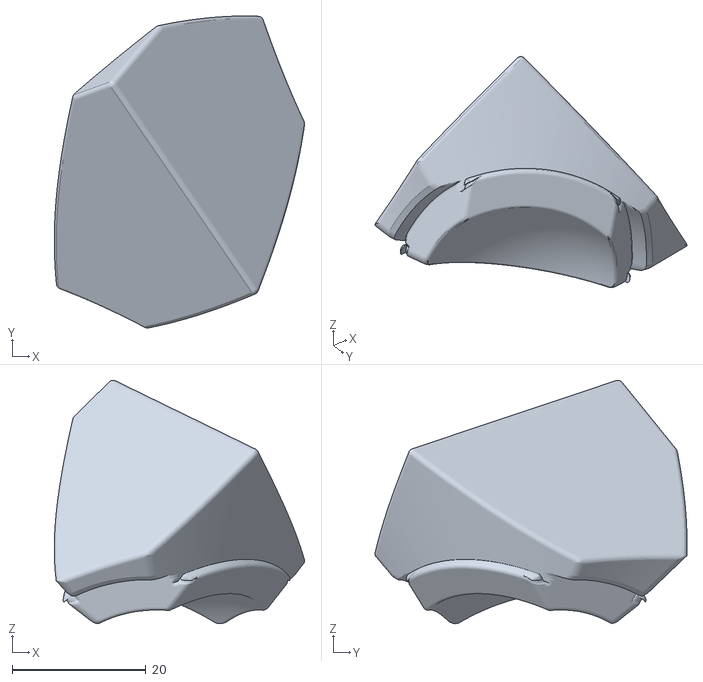
[picture p108: CAD file, 2026-09-27]
designs/triangular-prism-v1/stl/puzzle/H01.stl
37.5 x 46.7 x 36.5
