lukacslacko/wonkycube/designs/wavy-redi-v1.1/plates/core-and-axles-01.3mf

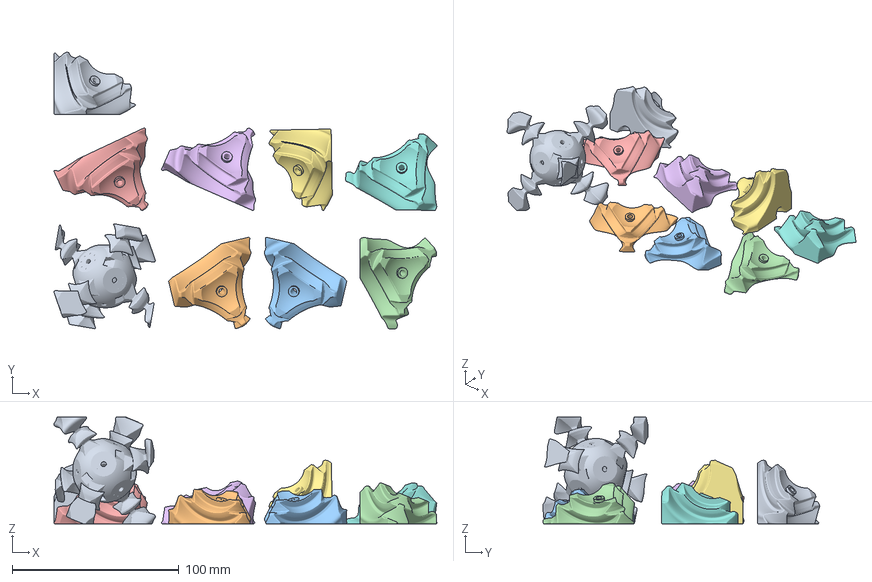
[picture p109: CAD file, 2026-09-23]
designs/wavy-redi-v1.1/plates/core-and-axles-01.3mf
229.6 x 165.8 x 64.0 mm
core
C01
C08
C06
C04
C05
C07
C03
C02
