lukacslacko/wonkycube/designs/wavy-redi-v1.1/stl/puzzle/E05.stl

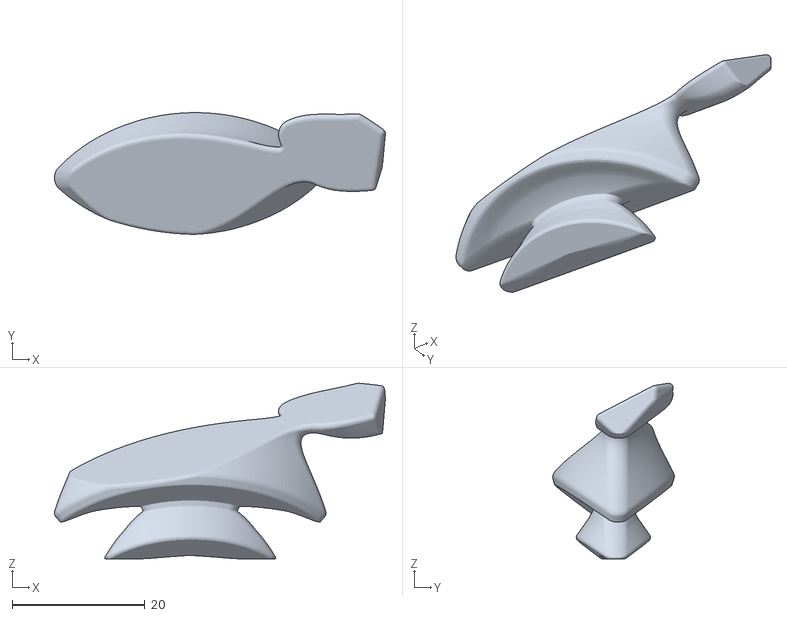
[picture p110: CAD file, 2026-09-23]
designs/wavy-redi-v1.1/stl/puzzle/E05.stl
49.9 x 18.3 x 26.5
