lukacslacko/wonkycube/models/current/plates/edges_07_to_12.3mf

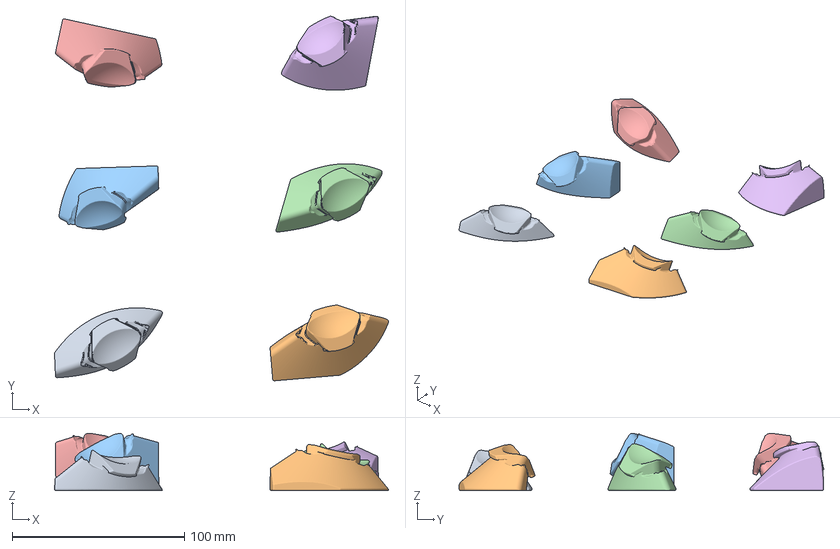
[picture p111: CAD file, 2026-09-14]
models/current/plates/edges_07_to_12.3mf
193.7 x 211.4 x 33.3 mm
E07
E08
E09
E10
E11
E12
