lukacslacko/wonkycube/cad/baseline/calibration/test_fixture.stl

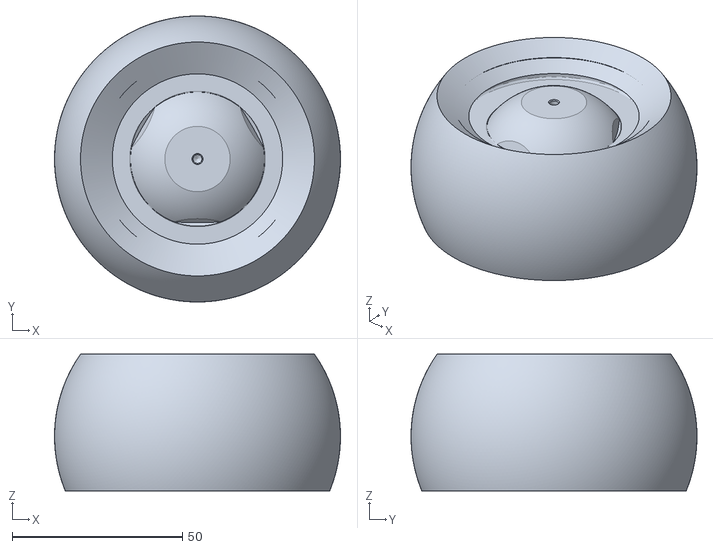
[picture p112: CAD file, 2026-09-14]
cad/baseline/calibration/test_fixture.stl
84.0 x 84.0 x 40.2
