lukacslacko/wonkycube/designs/conical-3x3-v1.1/print-options/K08-radial-down.3mf

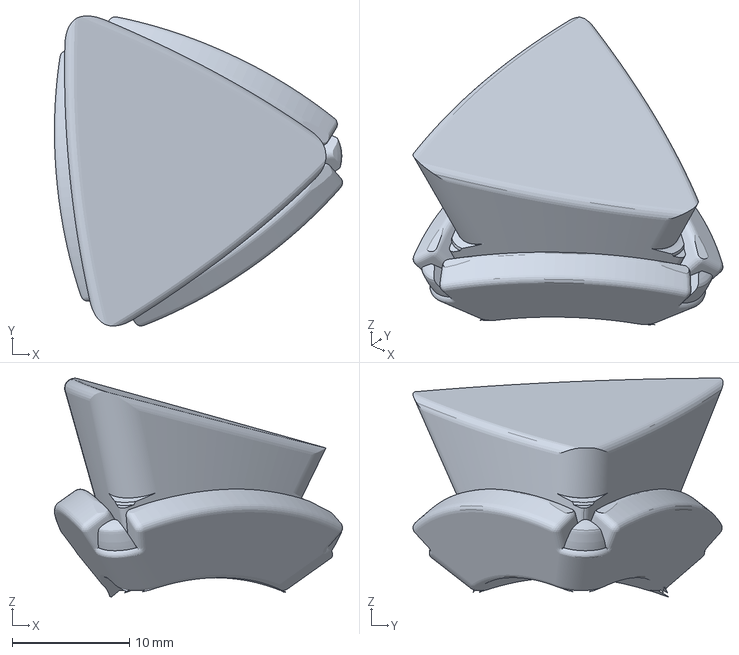
[picture p113: CAD file, 2026-09-18]
designs/conical-3x3-v1.1/print-options/K08-radial-down.3mf
24.6 x 26.5 x 18.7 mm
