lukacslacko/wonkycube/designs/curvy-copter-cuboctahedron-v3.2/plates/P-01.3mf

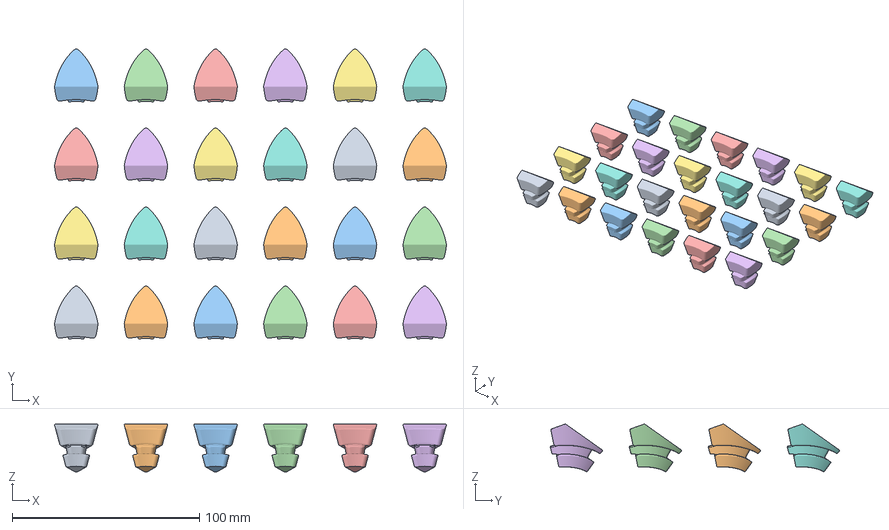
[picture p114: CAD file, 2026-09-29]
designs/curvy-copter-cuboctahedron-v3.2/plates/P-01.3mf
209.5 x 154.9 x 25.6 mm
P01
P02
P03
P04
P05
P06
P07
P08
P09
P10
P11
P12
P13
P14
P15
P16
P17
P18
P19
P20
P21
P22
P23
P24
