lukacslacko/wonkycube/designs/double-ivy-v7.1/plates/E-01.3mf

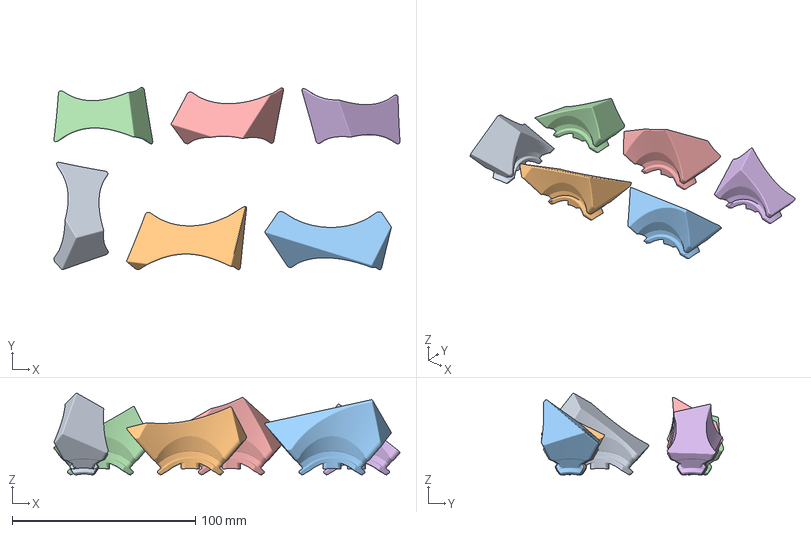
[picture p115: CAD file, 2026-09-30]
designs/double-ivy-v7.1/plates/E-01.3mf
188.6 x 99.5 x 44.5 mm
E03
E06
E05
E01
E04
E02
