lukacslacko/wonkycube/designs/double-ivy-v7.1/stl/puzzle/E04.stl

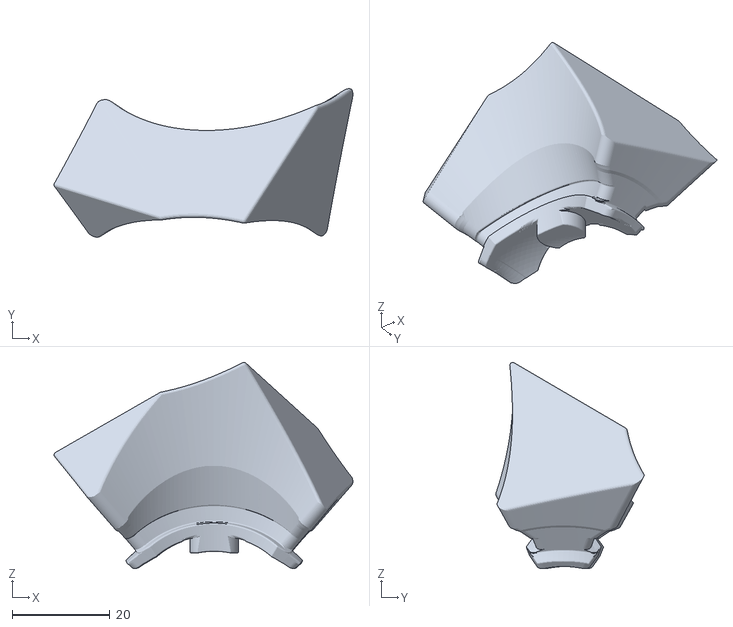
[picture p116: CAD file, 2026-09-30]
designs/double-ivy-v7.1/stl/puzzle/E04.stl
61.3 x 30.5 x 42.3
