lukacslacko/wonkycube/designs/face-turning-cuboctahedron-v1/stl/puzzle/square-center-print-6.stl

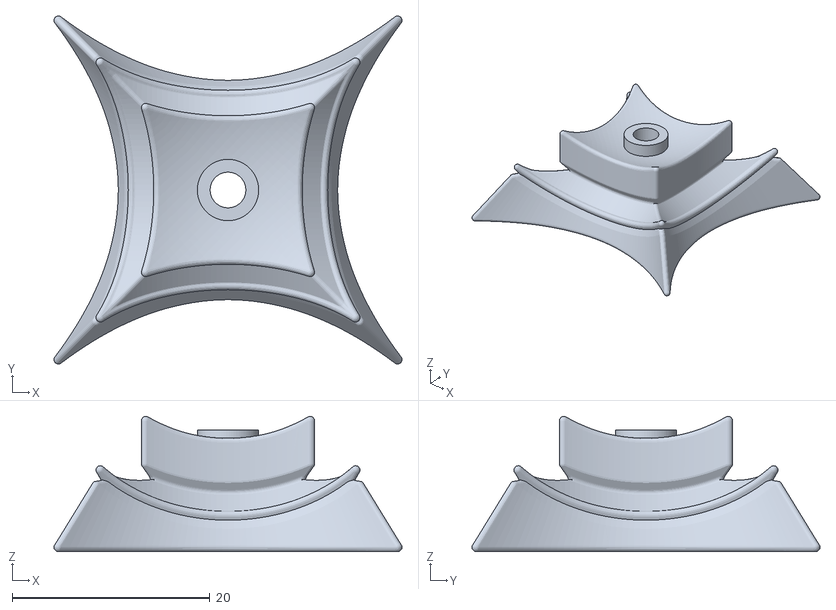
[picture p117: CAD file, 2026-09-28]
designs/face-turning-cuboctahedron-v1/stl/puzzle/square-center-print-6.stl
35.2 x 35.2 x 13.7
