lukacslacko/wonkycube/designs/pentagonal-prism-v1/plates/C-01.3mf

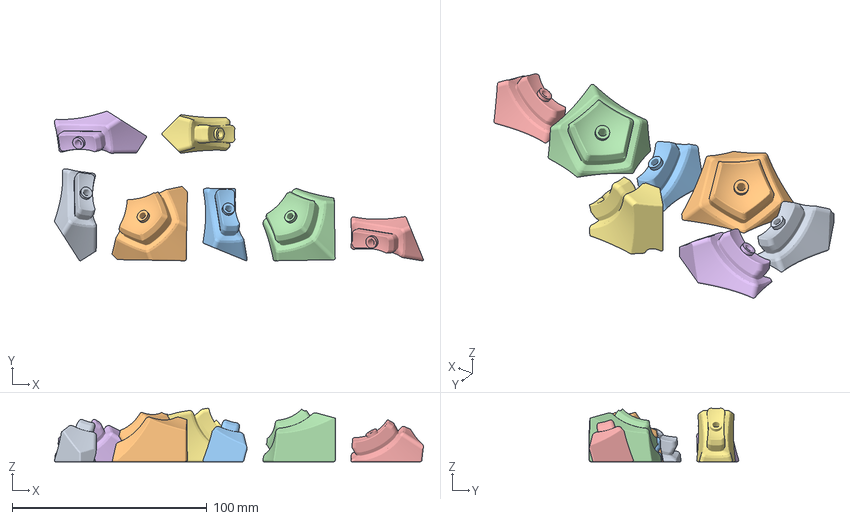
[picture p118: CAD file, 2026-09-23]
designs/pentagonal-prism-v1/plates/C-01.3mf
189.7 x 76.9 x 27.6 mm
C04
C07
C02
C06
C03
C01
C05
