lukacslacko/wonkycube/designs/pentagonal-prism-v1/print-options/H05-face-down.3mf

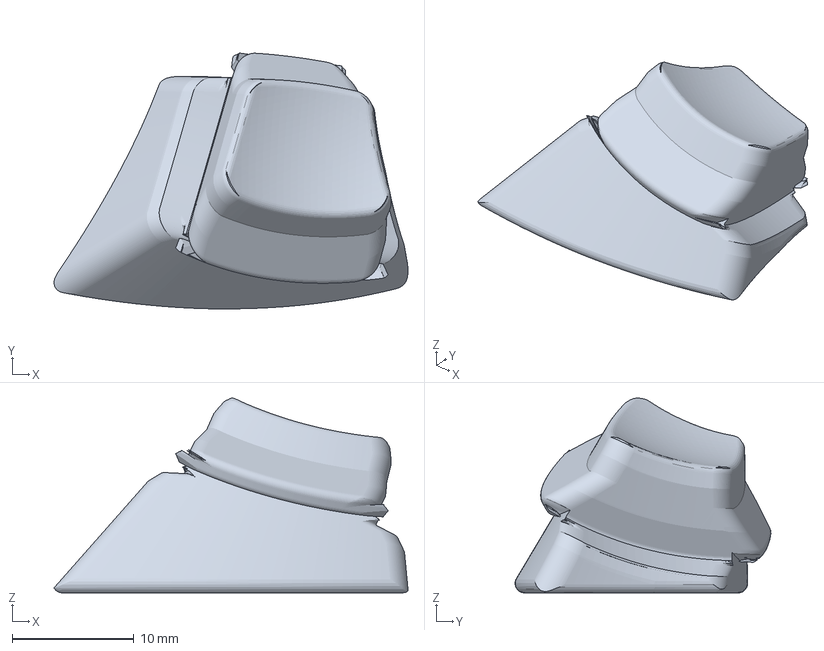
[picture p119: CAD file, 2026-09-23]
designs/pentagonal-prism-v1/print-options/H05-face-down.3mf
29.1 x 21.0 x 16.0 mm
