lukacslacko/wonkycube/designs/pentagonal-prism-v1/stl/puzzle/K09.stl

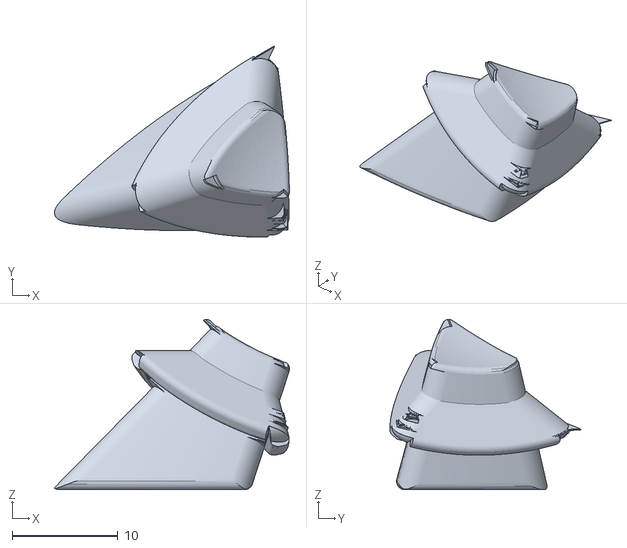
[picture p120: CAD file, 2026-09-23]
designs/pentagonal-prism-v1/stl/puzzle/K09.stl
22.2 x 18.1 x 16.1
