lukacslacko/wonkycube/designs/redi-v4.3/plates/core-01.3mf

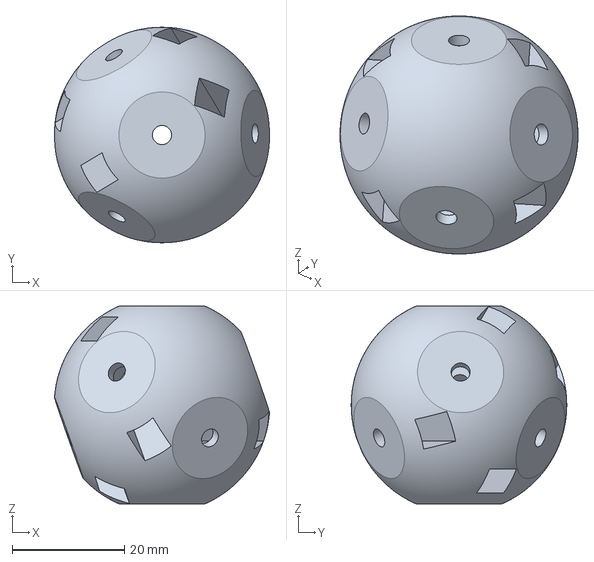
[picture p121: CAD file, 2026-09-17]
designs/redi-v4.3/plates/core-01.3mf
38.3 x 38.4 x 35.2 mm
