lukacslacko/wonkycube/designs/rhombic-dodecahedron-v5.1/inlays/fit-test/foam-size-options.dxf

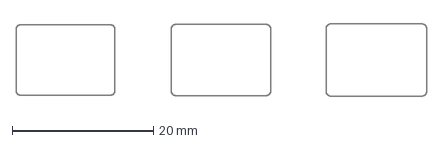
[picture p122: CAD file, 2026-10-06]
designs/rhombic-dodecahedron-v5.1/inlays/fit-test/foam-size-options.dxf
58.1 x 10.2 mm
