lukacslacko/wonkycube/designs/rhombic-dodecahedron-v5.1/inlays/fit-variants/easy/easy-F03.dxf

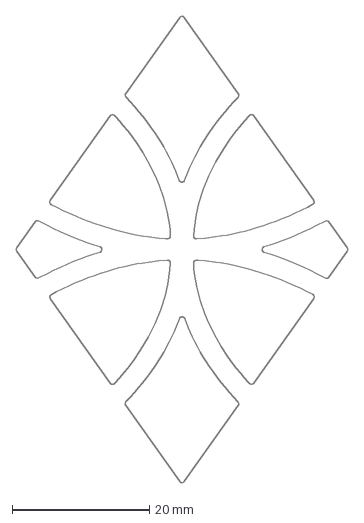
[picture p123: CAD file, 2026-10-06]
designs/rhombic-dodecahedron-v5.1/inlays/fit-variants/easy/easy-F03.dxf
48.2 x 67.9 mm
