lukacslacko/wonkycube/designs/rhombic-dodecahedron-v5.1/inlays/fit-variants/firm/firm-F08.dxf

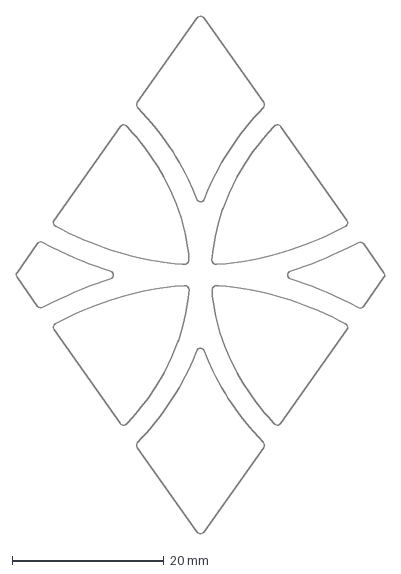
[picture p124: CAD file, 2026-10-06]
designs/rhombic-dodecahedron-v5.1/inlays/fit-variants/firm/firm-F08.dxf
48.5 x 68.2 mm
