lukacslacko/wonkycube/designs/rhombic-dodecahedron-v5.1/plates/centers-core-01.3mf

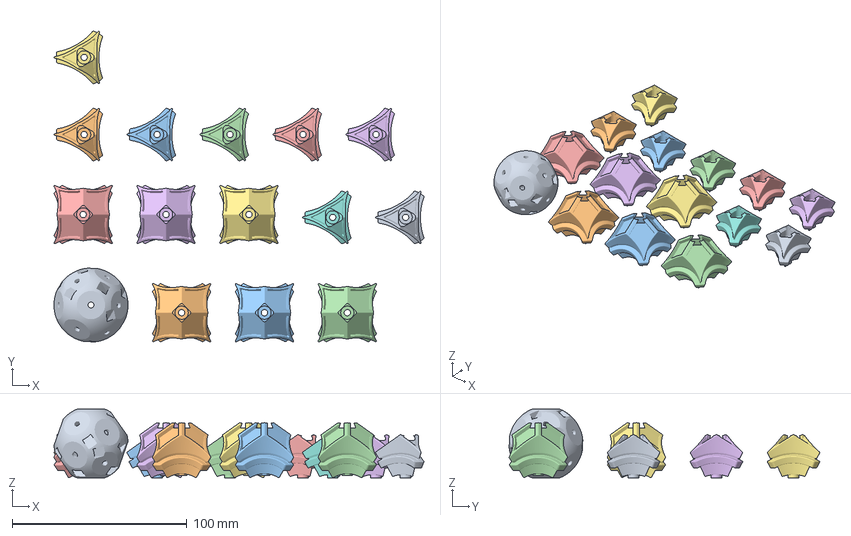
[picture p125: CAD file, 2026-10-06]
designs/rhombic-dodecahedron-v5.1/plates/centers-core-01.3mf
211.7 x 177.9 x 39.2 mm
core
S01
S02
S03
S04
S05
S06
T01
T02
T03
T04
T05
T06
T07
T08
