lukacslacko/wonkycube/designs/rhombic-dodecahedron-v5.1/reference/DO-NOT-PRINT-with-inlays.3mf

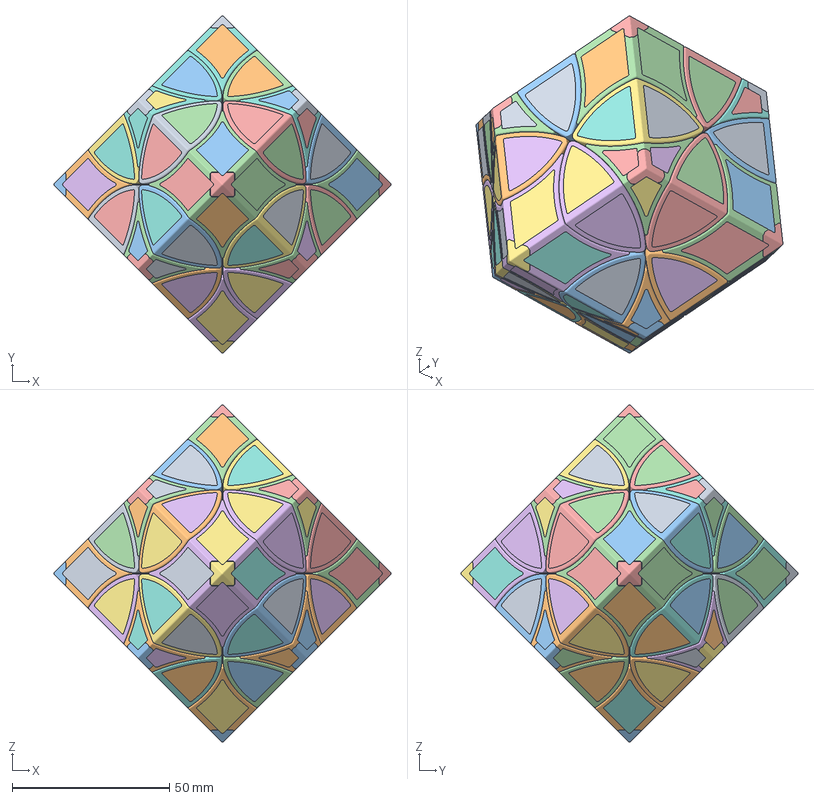
[picture p126: CAD file, 2026-10-06]
designs/rhombic-dodecahedron-v5.1/reference/DO-NOT-PRINT-with-inlays.3mf
107.1 x 107.1 x 107.1 mm
core
T01
T01-cap
T02
T02-cap
T03
T03-cap
T04
T04-cap
T05
T05-cap
T06
T06-cap
T07
T07-cap
T08
T08-cap
S01
S01-cap
S02
S02-cap
S03
S03-cap
S04
S04-cap
S05
S05-cap
S06
S06-cap
P01
P02
P03
P04
P05
P06
P07
P08
P09
P10
P11
P12
P13
P14
P15
P16
P17
P18
P19
P20
P21
P22
P23
P24
inlay0
inlay1
inlay2
inlay3
inlay4
inlay5
inlay6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
