lukacslacko/wonkycube/designs/rhombic-dodecahedron-v5.1/stl/fit-coupons/foam-pocket-test.stl

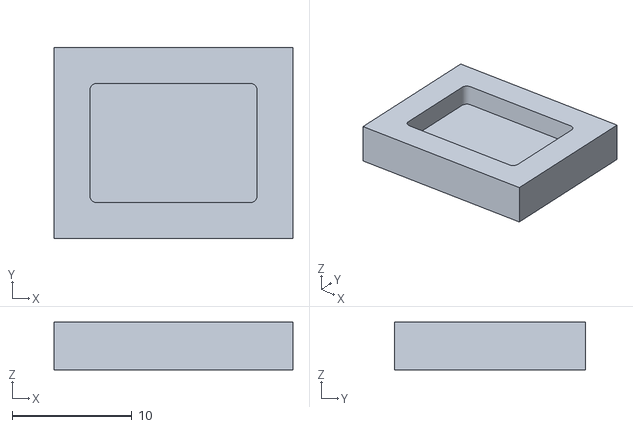
[picture p127: CAD file, 2026-10-06]
designs/rhombic-dodecahedron-v5.1/stl/fit-coupons/foam-pocket-test.stl
20.0 x 16.0 x 4.00
