lukacslacko/wonkycube/designs/rhombic-dodecahedron-v5.1/stl/puzzle/fourfold-plug-print-6.stl

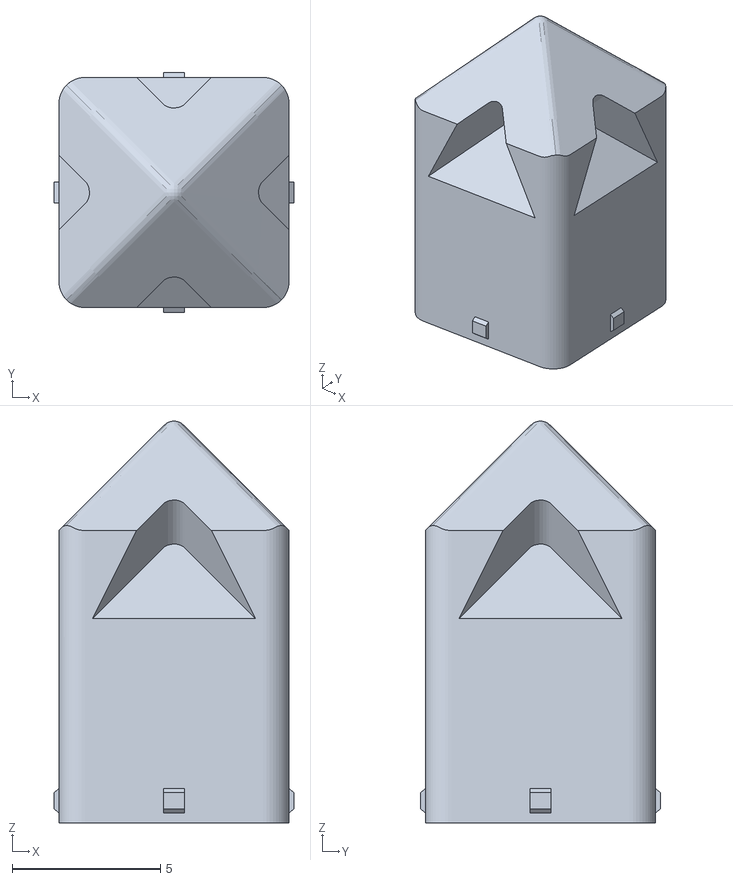
[picture p128: CAD file, 2026-10-06]
designs/rhombic-dodecahedron-v5.1/stl/puzzle/fourfold-plug-print-6.stl
8.08 x 8.08 x 13.6
