lukacslacko/wonkycube/designs/skewb-v1.1/plates/fit-coupons-01.3mf

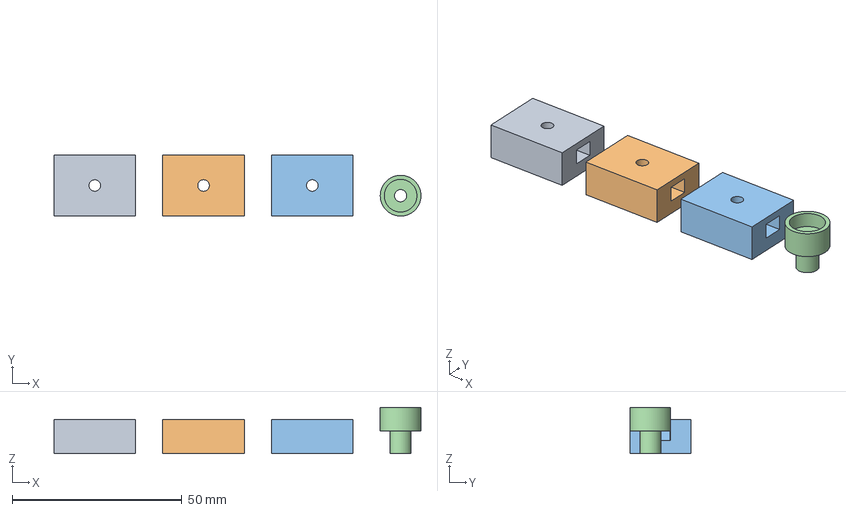
[picture p129: CAD file, 2026-09-18]
designs/skewb-v1.1/plates/fit-coupons-01.3mf
108.0 x 18.0 x 13.6 mm
nut-fit-5.30
nut-fit-5.40
nut-fit-5.50
rotor-fit
