lukacslacko/wonkycube/designs/skewb-v1.1/print-options/F03-face-down.3mf

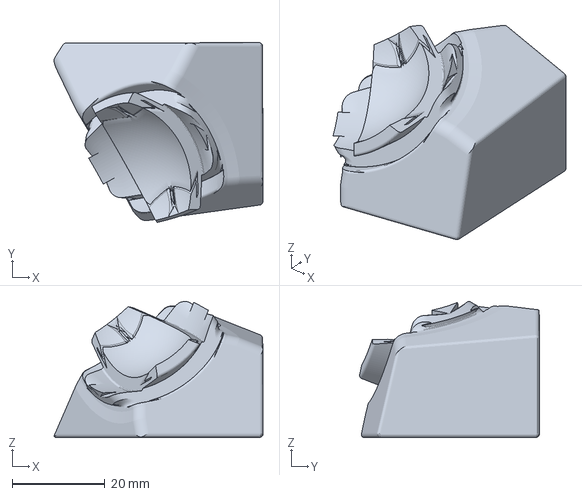
[picture p130: CAD file, 2026-09-18]
designs/skewb-v1.1/print-options/F03-face-down.3mf
45.0 x 38.7 x 29.3 mm
