lukacslacko/wonkycube/designs/skewb-v1.1/stl/puzzle/K03.stl

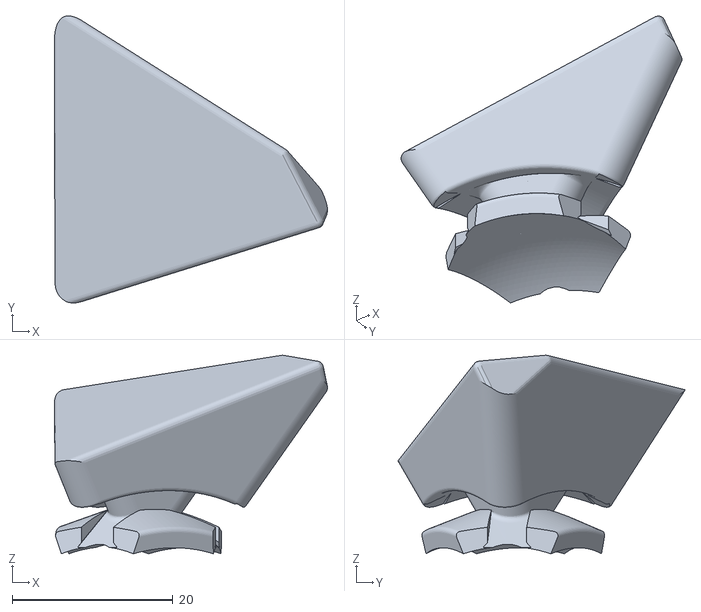
[picture p131: CAD file, 2026-09-18]
designs/skewb-v1.1/stl/puzzle/K03.stl
34.0 x 35.7 x 24.7
