lukacslacko/wonkycube/designs/triangular-prism-v1/print-options/K02-radial-down.3mf

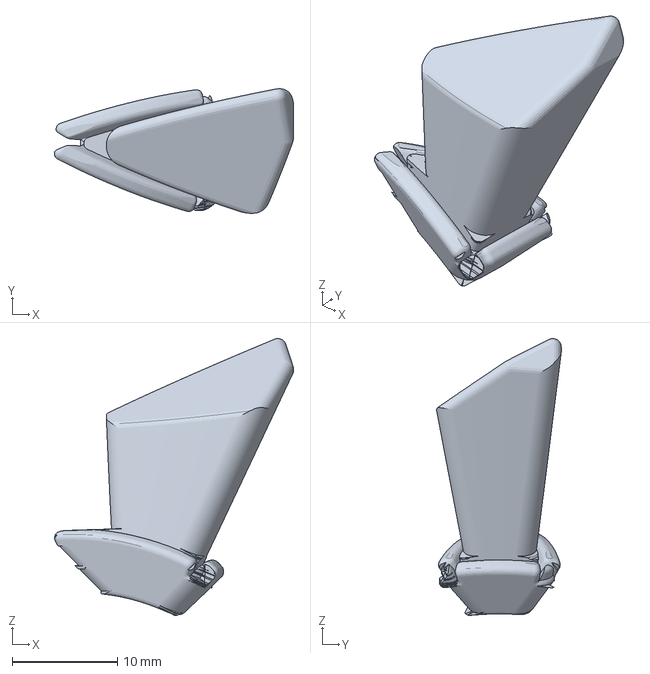
[picture p132: CAD file, 2026-09-27]
designs/triangular-prism-v1/print-options/K02-radial-down.3mf
22.7 x 11.8 x 26.3 mm
