lukacslacko/wonkycube/designs/triangular-prism-v1/stl/puzzle/H05.stl

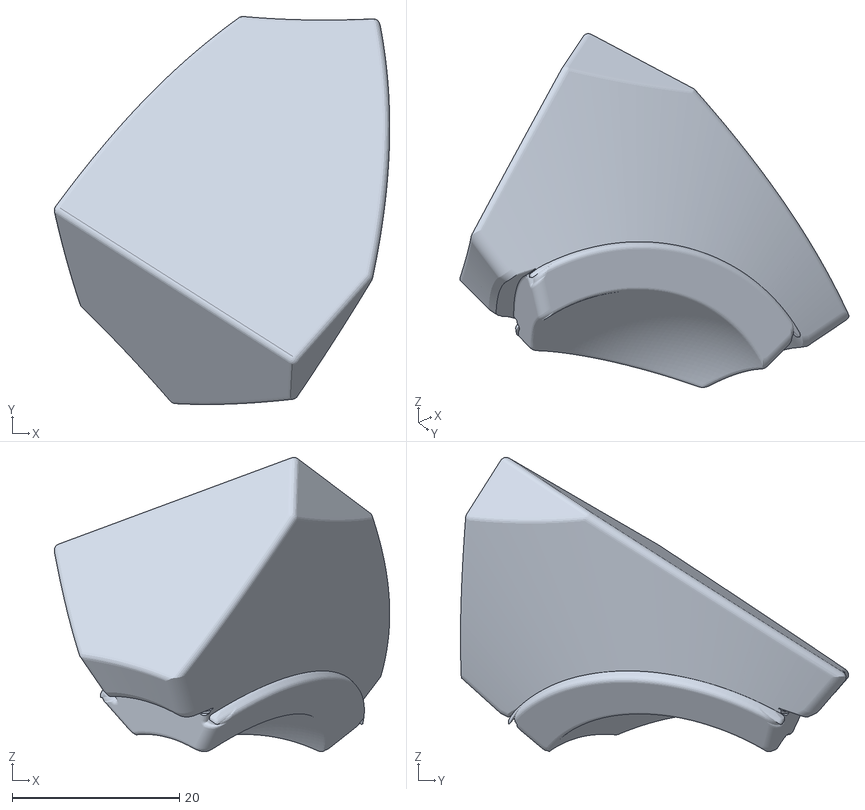
[picture p133: CAD file, 2026-09-27]
designs/triangular-prism-v1/stl/puzzle/H05.stl
40.1 x 46.4 x 35.1
