lukacslacko/wonkycube/designs/wavy-redi-v1.1/stl/puzzle/E07.stl

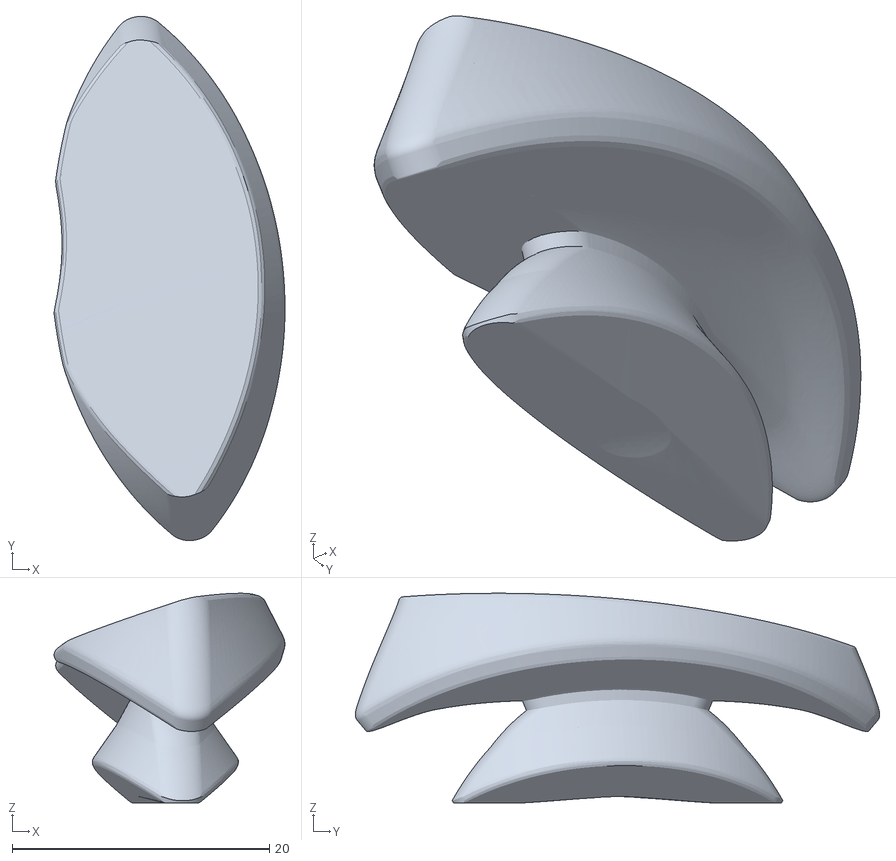
[picture p134: CAD file, 2026-09-23]
designs/wavy-redi-v1.1/stl/puzzle/E07.stl
18.0 x 40.7 x 16.3
