lukacslacko/wonkycube/models/current/calibration/fit_coupon.stl

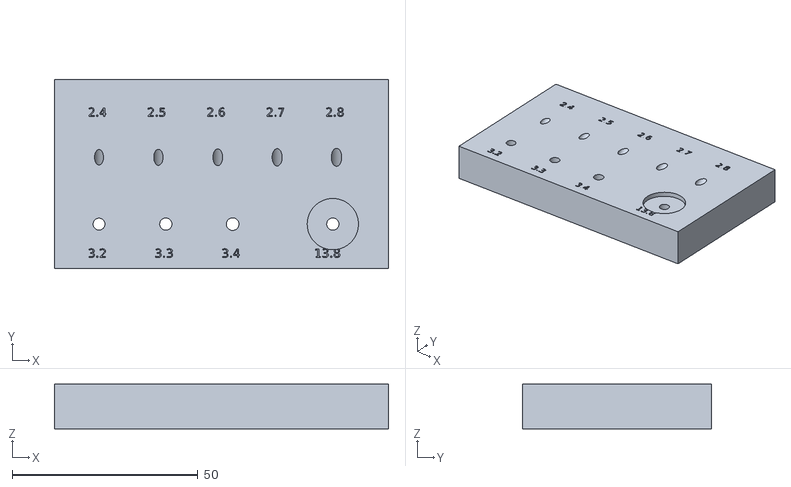
[picture p135: CAD file, 2026-09-14]
models/current/calibration/fit_coupon.stl
90.0 x 51.0 x 12.0
