lukacslacko/wonkycube/models/current/plates/core.3mf

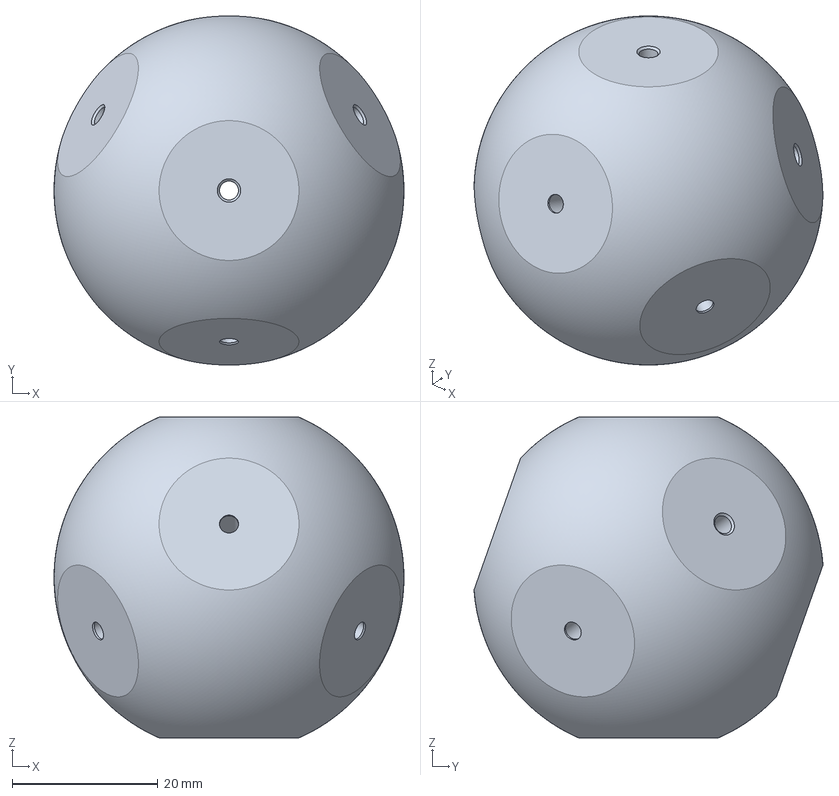
[picture p136: CAD file, 2026-09-14]
models/current/plates/core.3mf
48.0 x 47.9 x 44.0 mm
