lukacslacko/wonkycube/designs/conical-3x3-v1.1/print-options/E09-face-down.3mf

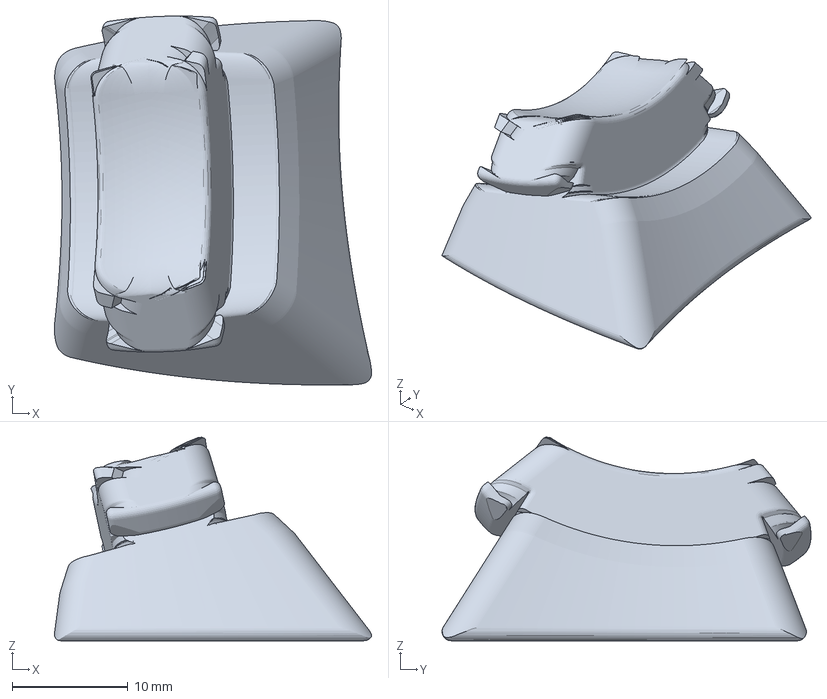
[picture p137: CAD file, 2026-09-18]
designs/conical-3x3-v1.1/print-options/E09-face-down.3mf
27.4 x 31.9 x 17.6 mm
