lukacslacko/wonkycube/designs/conical-3x3-v1.1/stl/optional/core-seat-5.50.stl

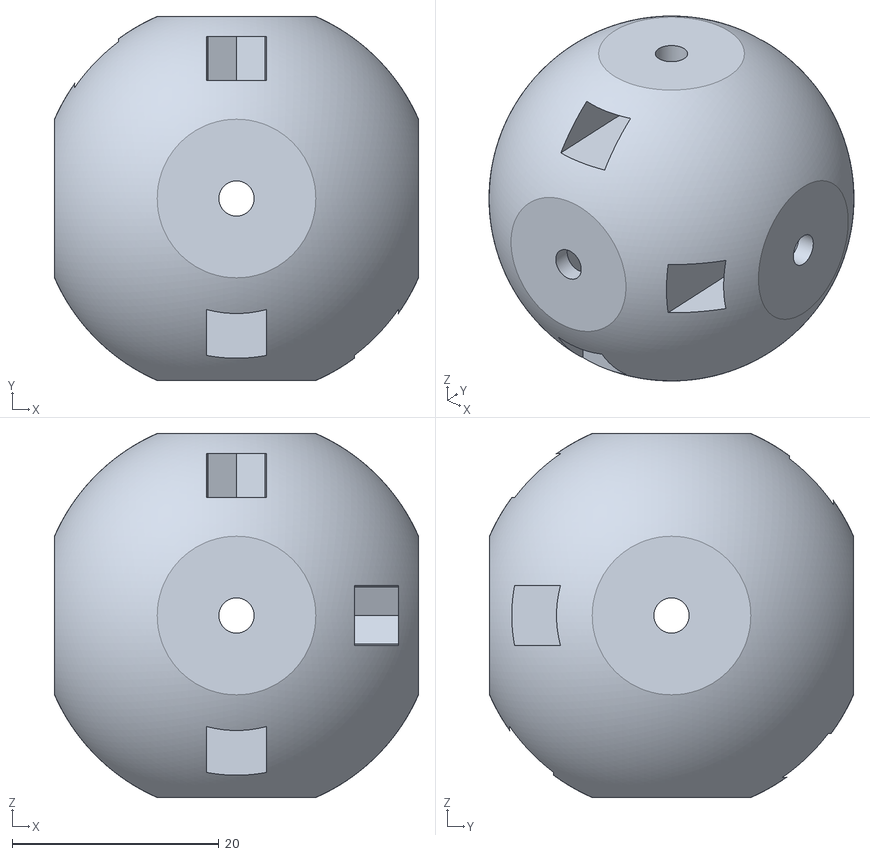
[picture p138: CAD file, 2026-09-18]
designs/conical-3x3-v1.1/stl/optional/core-seat-5.50.stl
35.2 x 35.2 x 35.2
