lukacslacko/wonkycube/designs/curvy-copter-cuboctahedron-v3.2/plates/K-01.3mf

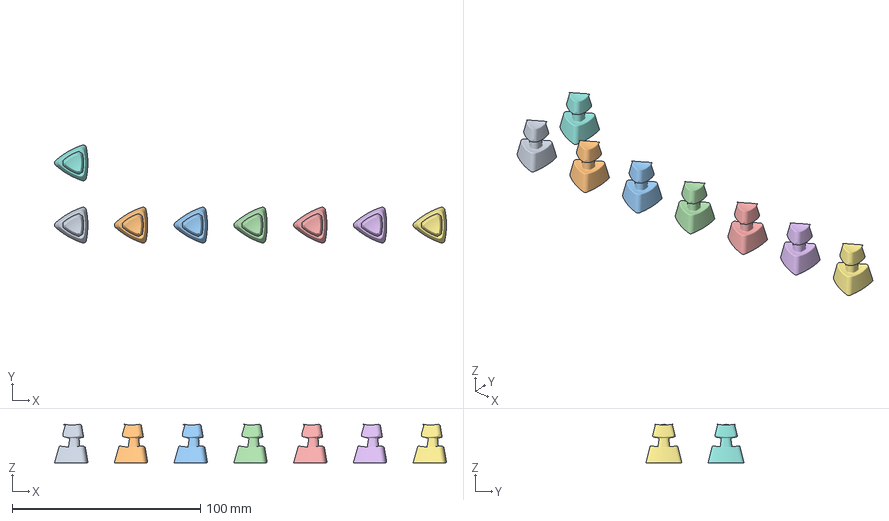
[picture p139: CAD file, 2026-09-29]
designs/curvy-copter-cuboctahedron-v3.2/plates/K-01.3mf
208.4 x 52.1 x 20.5 mm
K01
K02
K03
K04
K05
K06
K07
K08
