lukacslacko/wonkycube/designs/curvy-copter-cuboctahedron-v3.2/start-here/upgrade-test-6-pieces.3mf

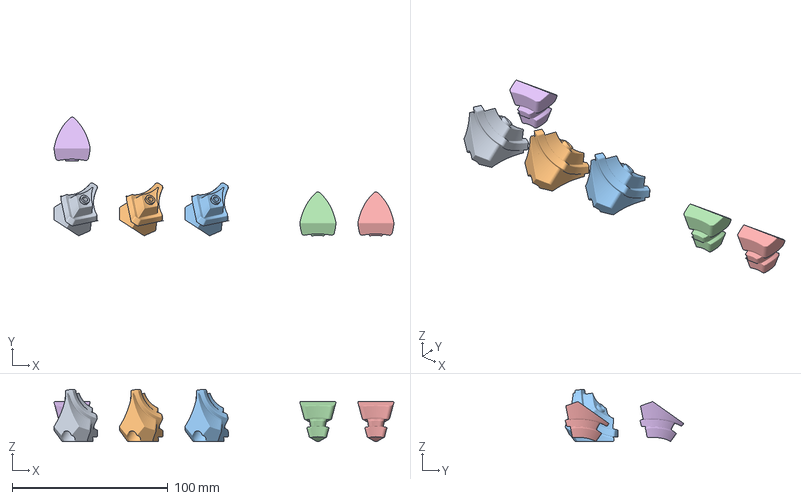
[picture p140: CAD file, 2026-09-29]
designs/curvy-copter-cuboctahedron-v3.2/start-here/upgrade-test-6-pieces.3mf
218.5 x 76.3 x 33.4 mm
C01
C02
C05
P01
P05
P06
