lukacslacko/wonkycube/designs/curvy-copter-cuboctahedron-v3.2/stl/puzzle/axial-center-print-12.stl

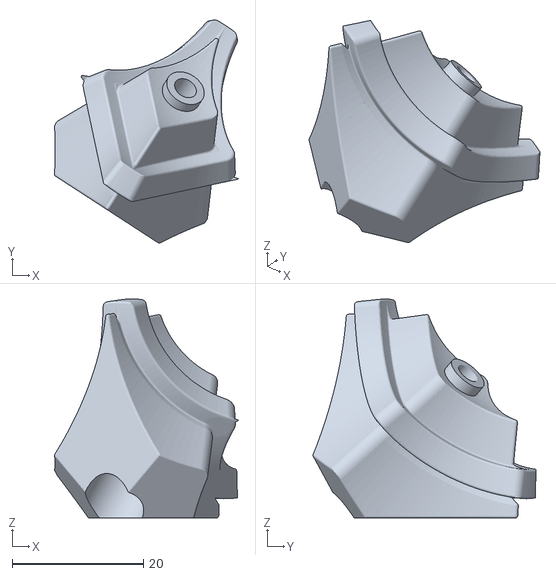
[picture p141: CAD file, 2026-09-29]
designs/curvy-copter-cuboctahedron-v3.2/stl/puzzle/axial-center-print-12.stl
28.1 x 34.1 x 33.4
