lukacslacko/wonkycube/designs/double-ivy-v7.1/plates/W-01.3mf

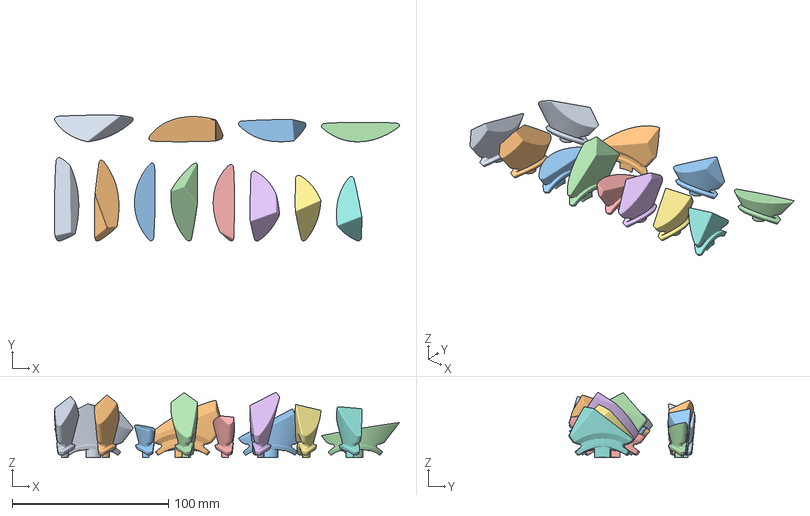
[picture p142: CAD file, 2026-09-30]
designs/double-ivy-v7.1/plates/W-01.3mf
221.0 x 80.5 x 41.7 mm
W12
W04
W11
W07
W05
W08
W02
W03
W10
W06
W01
W09
