lukacslacko/wonkycube/designs/double-ivy-v7.1/stl/puzzle/W07.stl

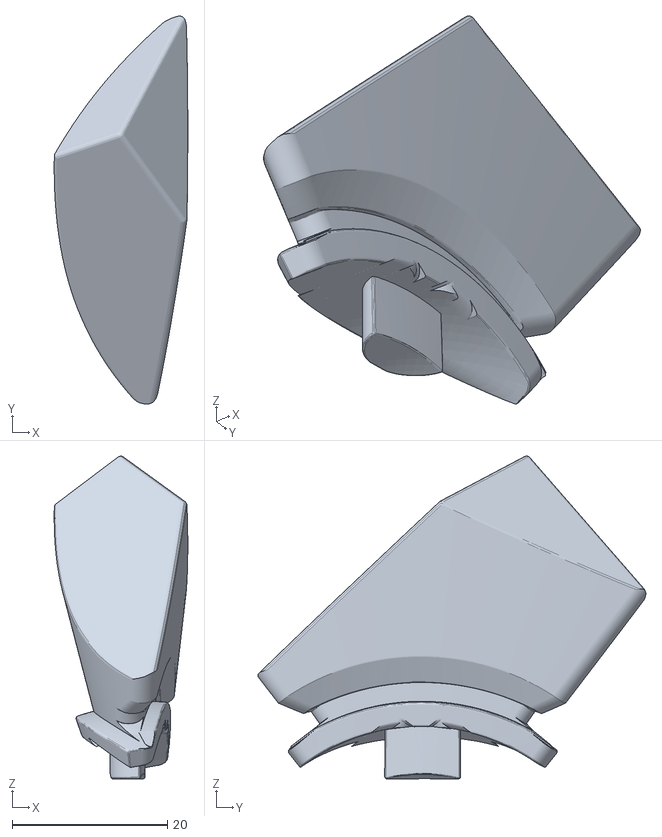
[picture p143: CAD file, 2026-09-30]
designs/double-ivy-v7.1/stl/puzzle/W07.stl
17.2 x 49.9 x 41.5
