lukacslacko/wonkycube/designs/face-turning-cuboctahedron-v1/stl/puzzle/petal-print-24.stl

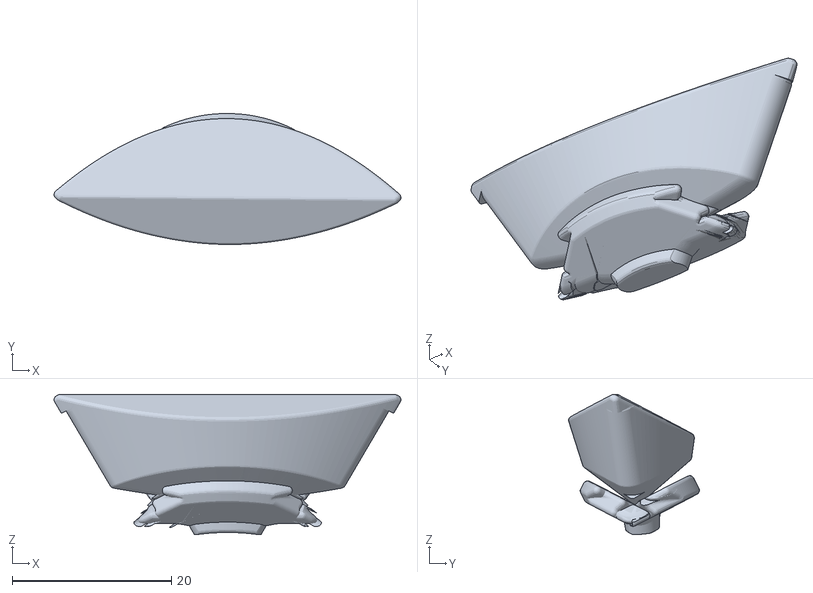
[picture p144: CAD file, 2026-09-28]
designs/face-turning-cuboctahedron-v1/stl/puzzle/petal-print-24.stl
43.6 x 16.4 x 17.6
