lukacslacko/wonkycube/designs/pentagonal-prism-v1/plates/K-01.3mf

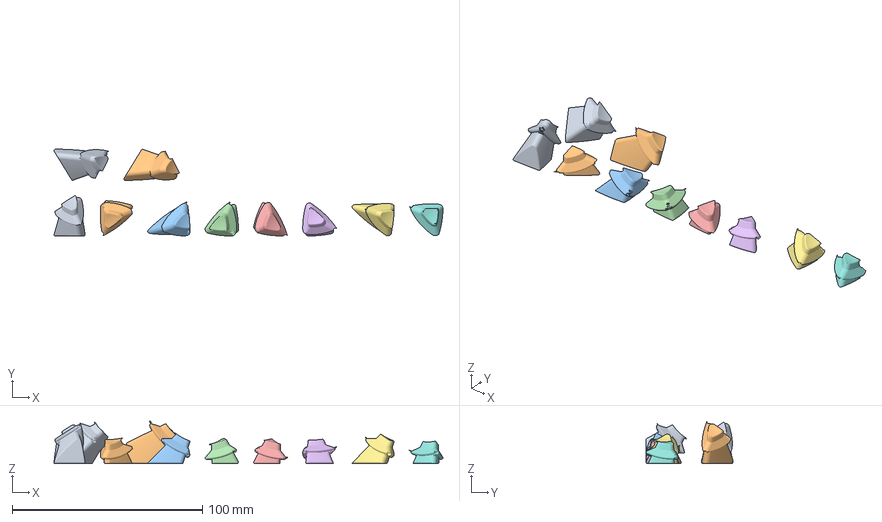
[picture p145: CAD file, 2026-09-23]
designs/pentagonal-prism-v1/plates/K-01.3mf
204.5 x 45.7 x 22.2 mm
K05
K01
K09
K07
K10
K04
K03
K06
K02
K08
