lukacslacko/wonkycube/designs/pentagonal-prism-v1/print-options/K03-radial-down.3mf

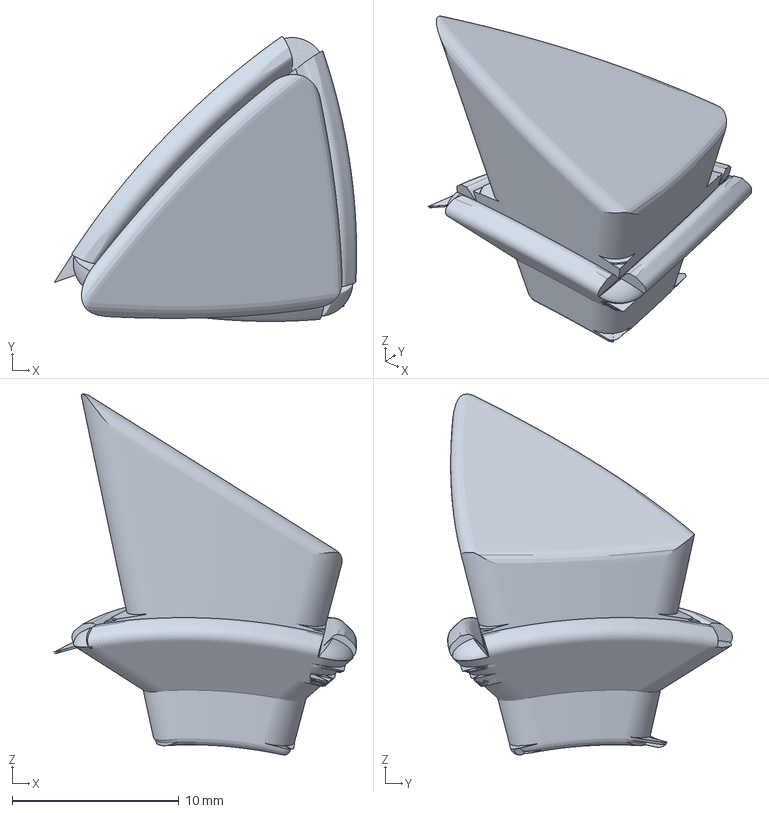
[picture p146: CAD file, 2026-09-23]
designs/pentagonal-prism-v1/print-options/K03-radial-down.3mf
18.1 x 17.1 x 21.7 mm
