lukacslacko/wonkycube/designs/pentagonal-prism-v1/stl/puzzle/H04.stl

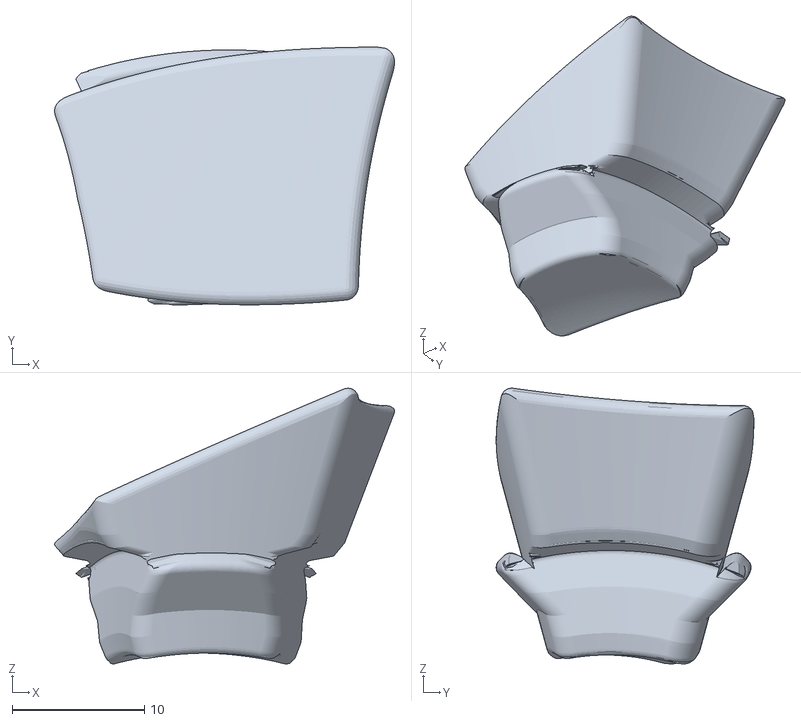
[picture p147: CAD file, 2026-09-23]
designs/pentagonal-prism-v1/stl/puzzle/H04.stl
25.7 x 19.5 x 20.8
