lukacslacko/wonkycube/designs/rhombic-dodecahedron-v5.1/plates/P-01.3mf

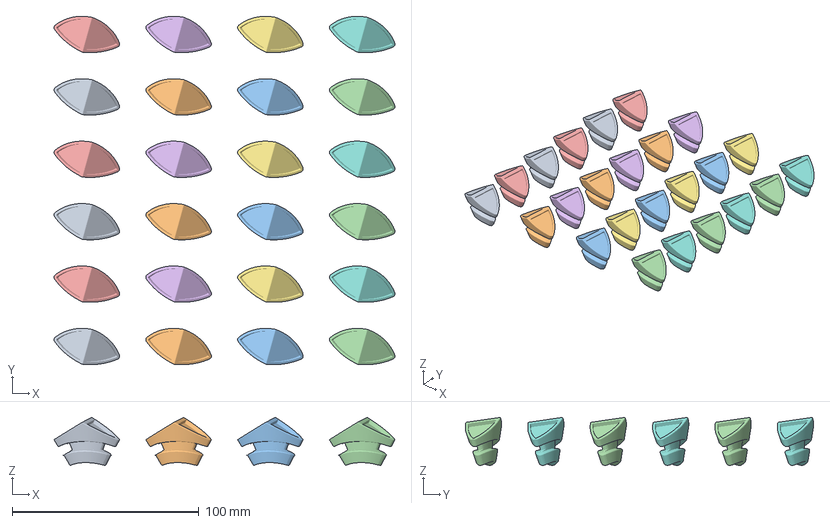
[picture p150: CAD file, 2026-10-06]
designs/rhombic-dodecahedron-v5.1/plates/P-01.3mf
182.6 x 186.6 x 25.7 mm
P01
P02
P03
P04
P05
P06
P07
P08
P09
P10
P11
P12
P13
P14
P15
P16
P17
P18
P19
P20
P21
P22
P23
P24
