lukacslacko/wonkycube/designs/rhombic-dodecahedron-v5.1/stl/fit-coupons/threefold-key-peg.stl

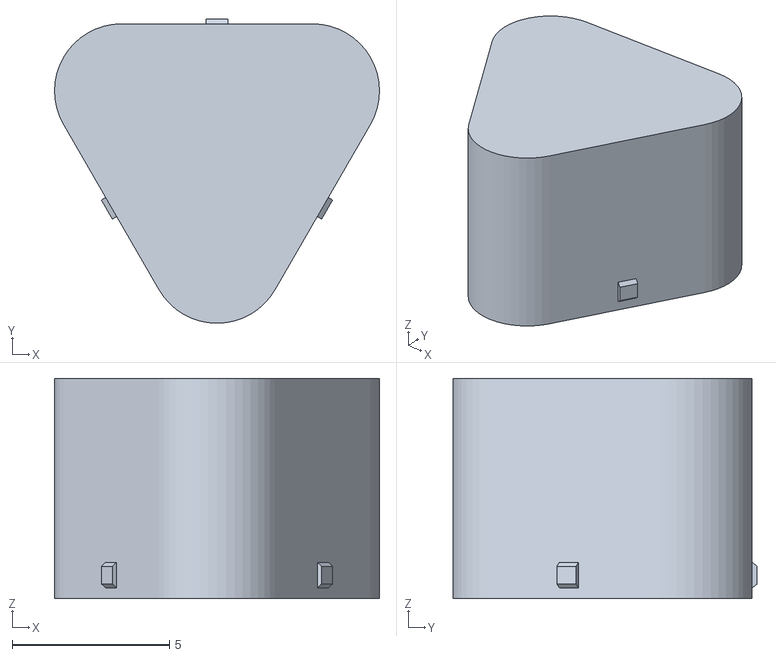
[picture p151: CAD file, 2026-10-06]
designs/rhombic-dodecahedron-v5.1/stl/fit-coupons/threefold-key-peg.stl
10.3 x 9.67 x 7.00
