lukacslacko/wonkycube/designs/rhombic-dodecahedron-v5.1/stl/puzzle/threefold-center-print-8.stl

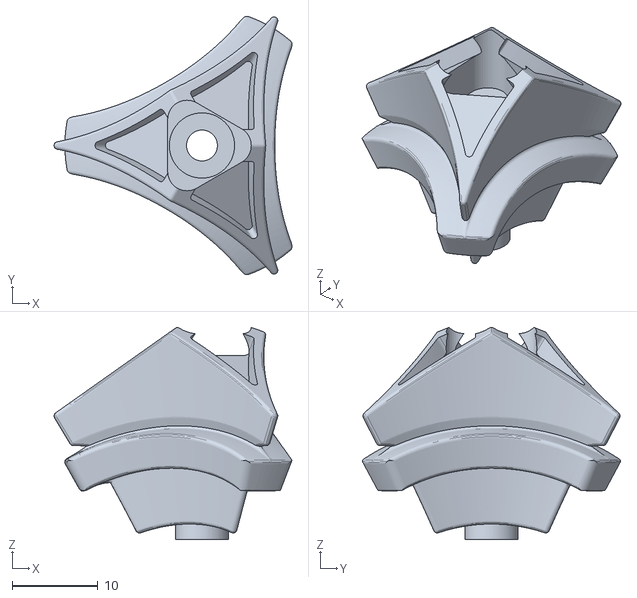
[picture p152: CAD file, 2026-10-06]
designs/rhombic-dodecahedron-v5.1/stl/puzzle/threefold-center-print-8.stl
27.8 x 30.1 x 24.7
