lukacslacko/wonkycube/designs/skewb-v1.1/plates/K-01.3mf

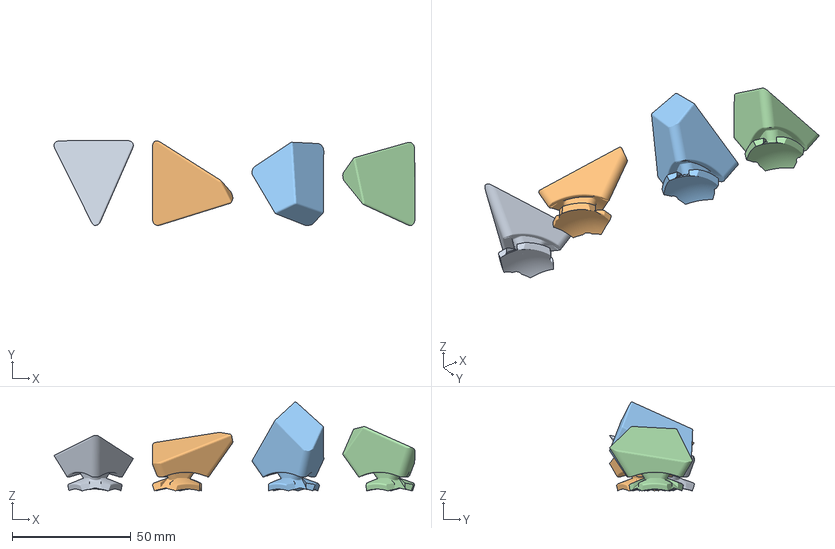
[picture p153: CAD file, 2026-09-18]
designs/skewb-v1.1/plates/K-01.3mf
152.2 x 35.8 x 37.5 mm
K01
K03
K04
K02
