lukacslacko/wonkycube/designs/skewb-v1.1/print-options/F01-face-down.3mf

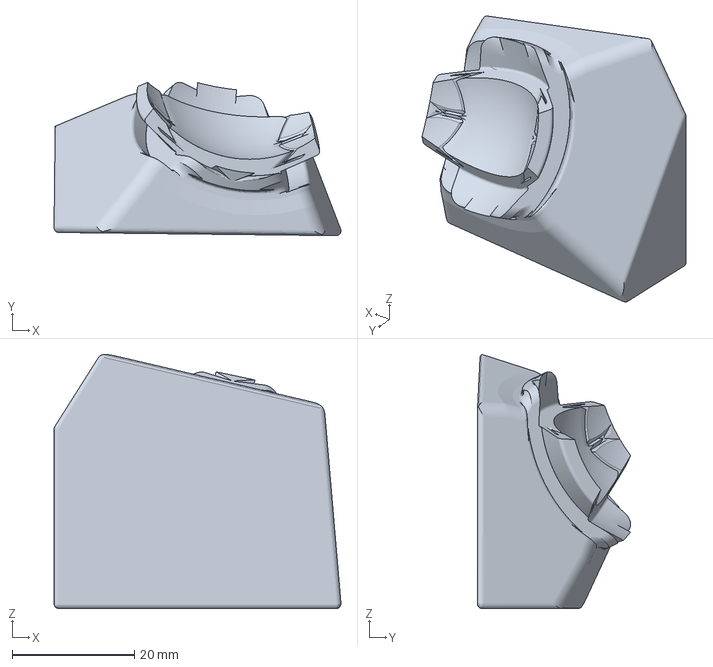
[picture p154: CAD file, 2026-09-18]
designs/skewb-v1.1/print-options/F01-face-down.3mf
47.0 x 25.1 x 41.6 mm
