lukacslacko/wonkycube/designs/skewb-v1.1/stl/puzzle/K02.stl

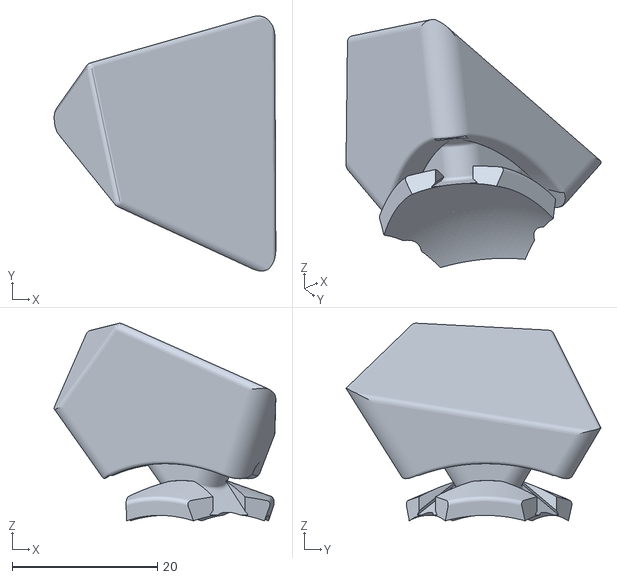
[picture p155: CAD file, 2026-09-18]
designs/skewb-v1.1/stl/puzzle/K02.stl
30.5 x 35.1 x 27.2
