lukacslacko/wonkycube/designs/triangular-prism-v1/plates/petals-01.3mf

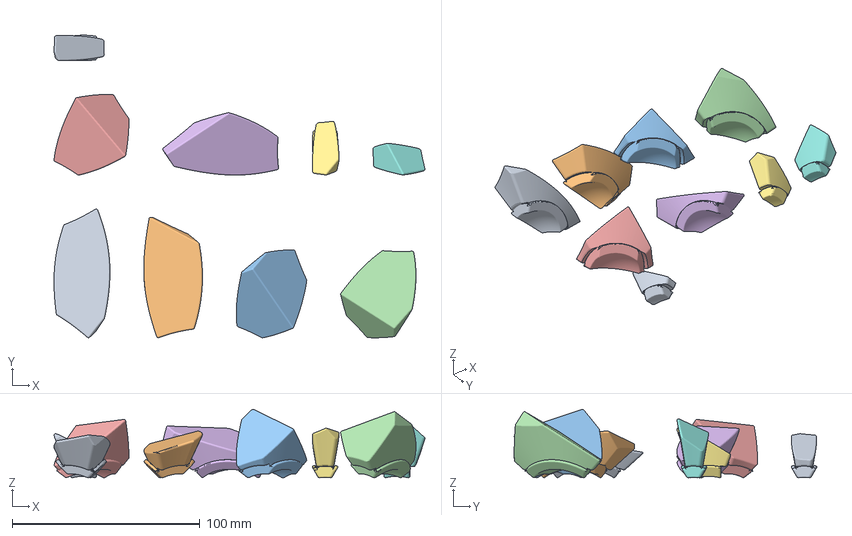
[picture p156: CAD file, 2026-09-27]
designs/triangular-prism-v1/plates/petals-01.3mf
197.3 x 161.0 x 36.5 mm
H04
H06
H01
H05
H03
H02
V03
V02
V01
