lukacslacko/wonkycube/designs/triangular-prism-v1/print-options/K05-radial-down.3mf

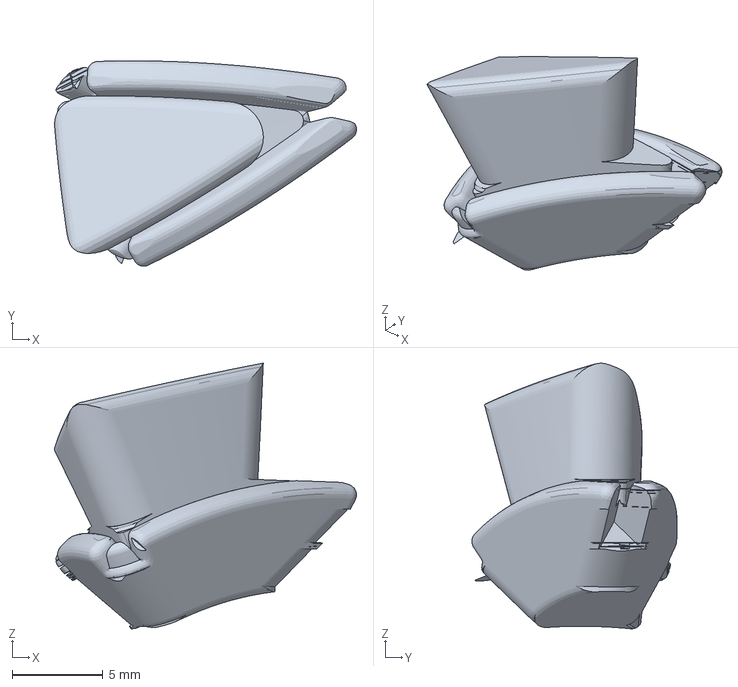
[picture p157: CAD file, 2026-09-27]
designs/triangular-prism-v1/print-options/K05-radial-down.3mf
16.7 x 11.3 x 14.7 mm
