lukacslacko/wonkycube/designs/triangular-prism-v1/stl/puzzle/H02.stl

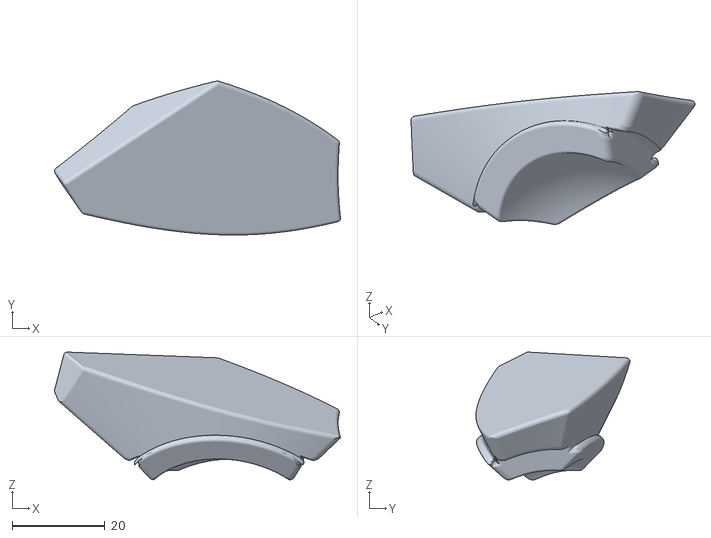
[picture p158: CAD file, 2026-09-27]
designs/triangular-prism-v1/stl/puzzle/H02.stl
61.6 x 33.2 x 27.5
