lukacslacko/wonkycube/designs/wavy-redi-v1.1/stl/puzzle/core.stl

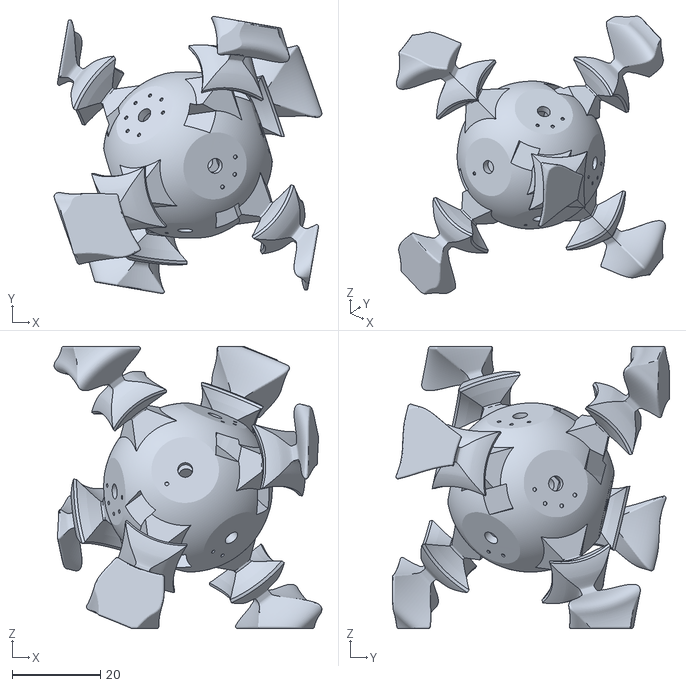
[picture p159: CAD file, 2026-09-23]
designs/wavy-redi-v1.1/stl/puzzle/core.stl
60.8 x 62.9 x 64.0
