lukacslacko/wonkycube/cad/baseline/calibration/test_edge_2.stl

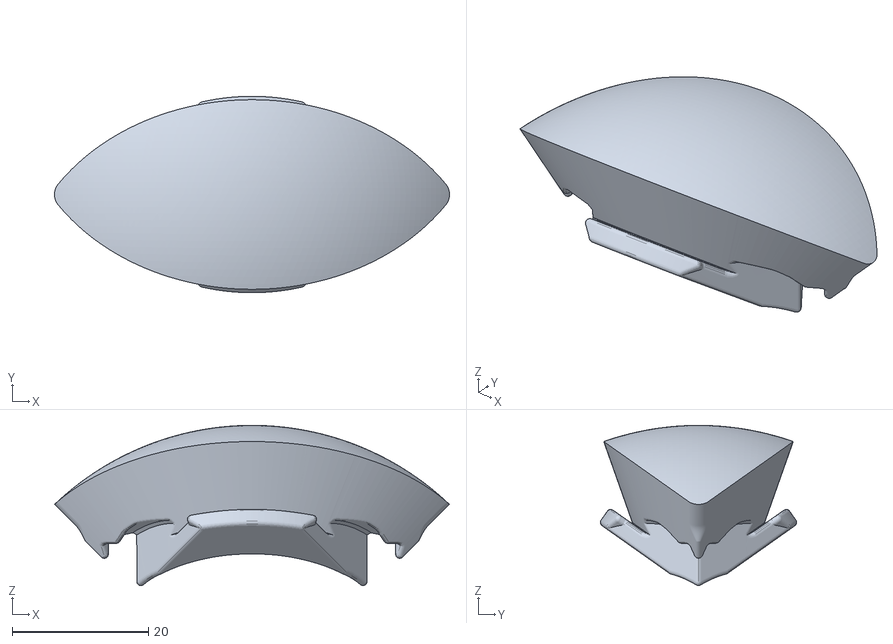
[picture p160: CAD file, 2026-09-14]
cad/baseline/calibration/test_edge_2.stl
57.9 x 28.8 x 23.5
