lukacslacko/wonkycube/designs/conical-3x3-v1.1/plates/E-01.3mf

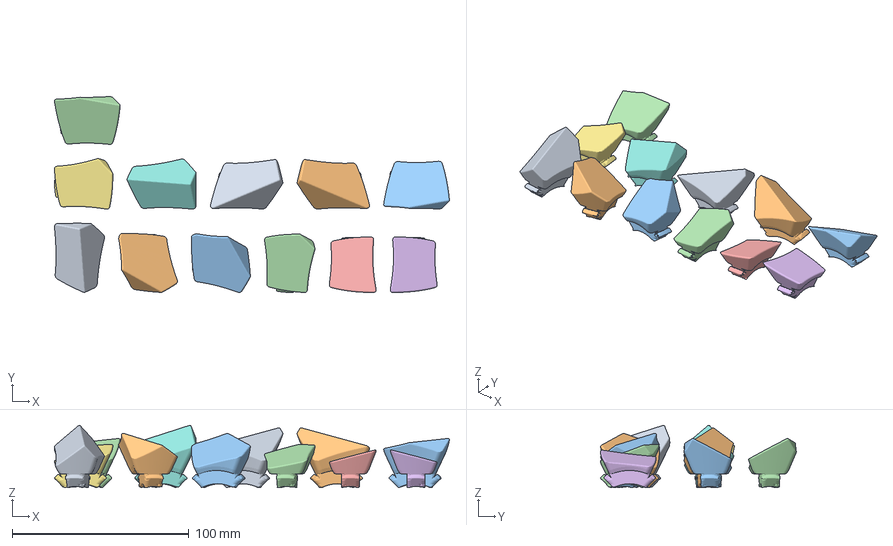
[picture p161: CAD file, 2026-09-18]
designs/conical-3x3-v1.1/plates/E-01.3mf
223.3 x 110.8 x 35.3 mm
E11
E10
E01
E08
E07
E09
E04
E02
E03
E06
E05
E12
