lukacslacko/wonkycube/designs/conical-3x3-v1.1/print-options/K05-radial-down.3mf

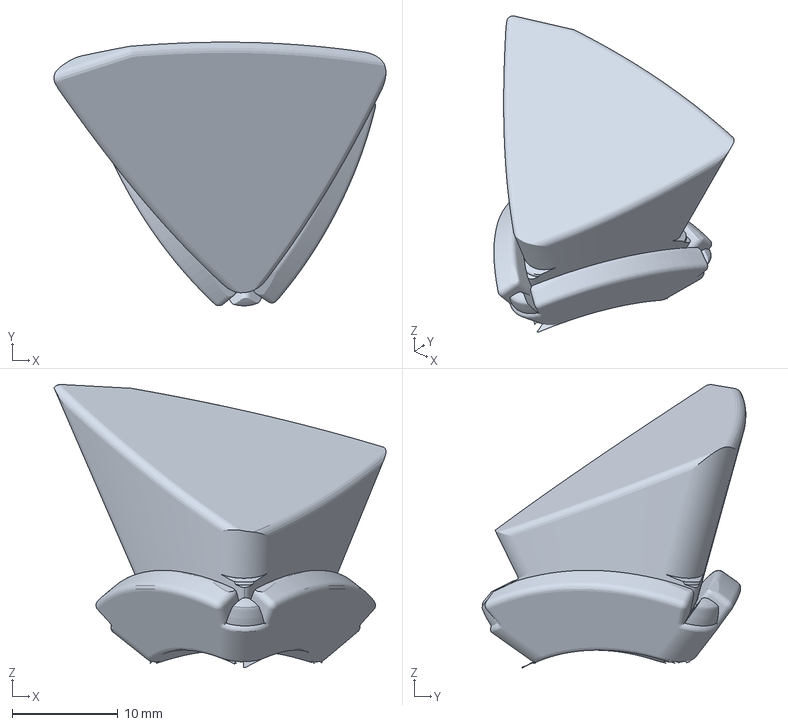
[picture p162: CAD file, 2026-09-18]
designs/conical-3x3-v1.1/print-options/K05-radial-down.3mf
31.4 x 25.0 x 26.8 mm
