lukacslacko/wonkycube/designs/curvy-copter-cuboctahedron-v3.2/start-here/centers-only-test-3-pieces.3mf

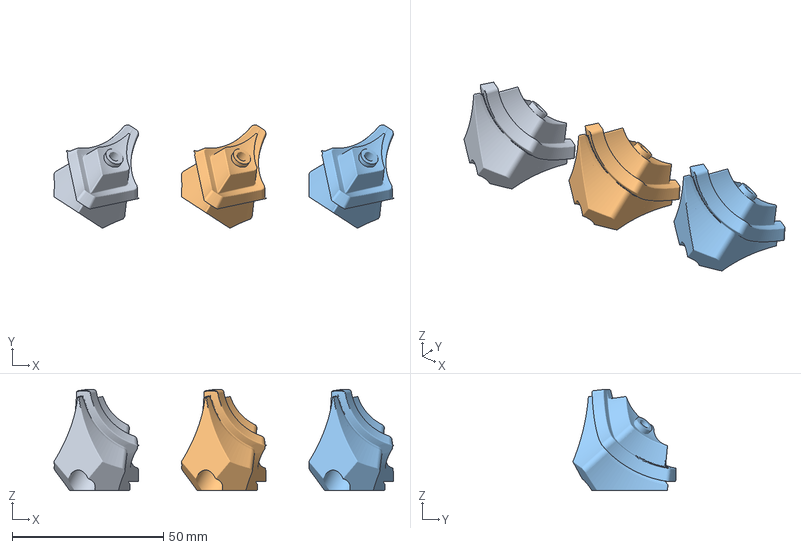
[picture p163: CAD file, 2026-09-29]
designs/curvy-copter-cuboctahedron-v3.2/start-here/centers-only-test-3-pieces.3mf
112.3 x 34.1 x 33.4 mm
C01
C02
C05
