lukacslacko/wonkycube/designs/curvy-copter-cuboctahedron-v3.2/stl/puzzle/petal-print-24.stl

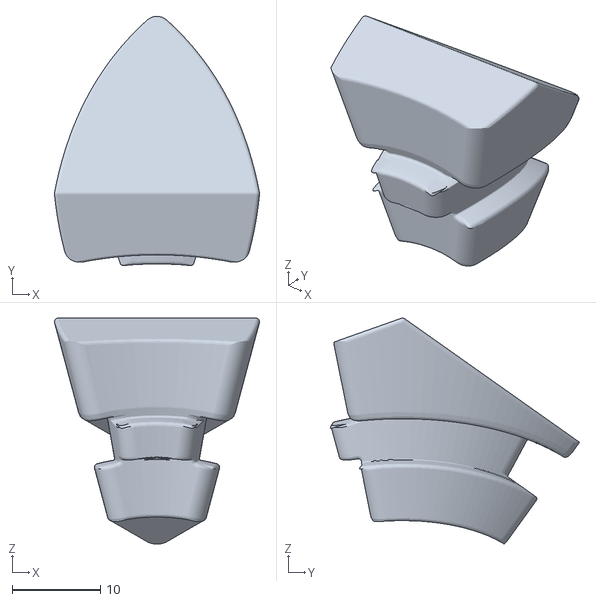
[picture p164: CAD file, 2026-09-29]
designs/curvy-copter-cuboctahedron-v3.2/stl/puzzle/petal-print-24.stl
23.3 x 28.2 x 25.6
