lukacslacko/wonkycube/designs/double-ivy-v7.1/stl/puzzle/W10.stl

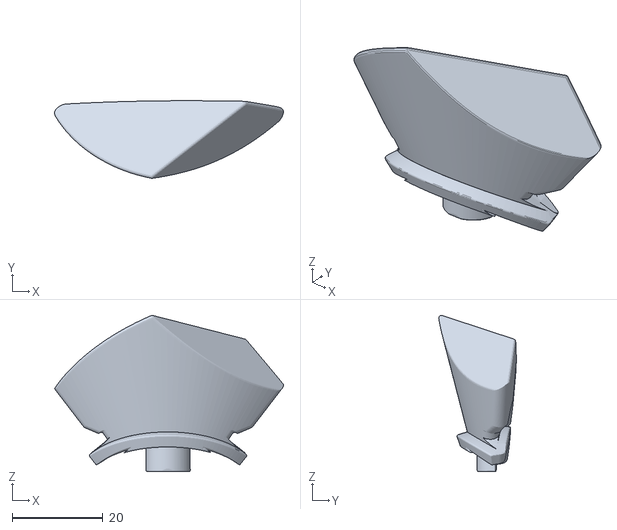
[picture p165: CAD file, 2026-09-30]
designs/double-ivy-v7.1/stl/puzzle/W10.stl
50.4 x 17.1 x 34.4
