lukacslacko/wonkycube/designs/curvy-copter-cuboctahedron-v3.2/images/assembly.png

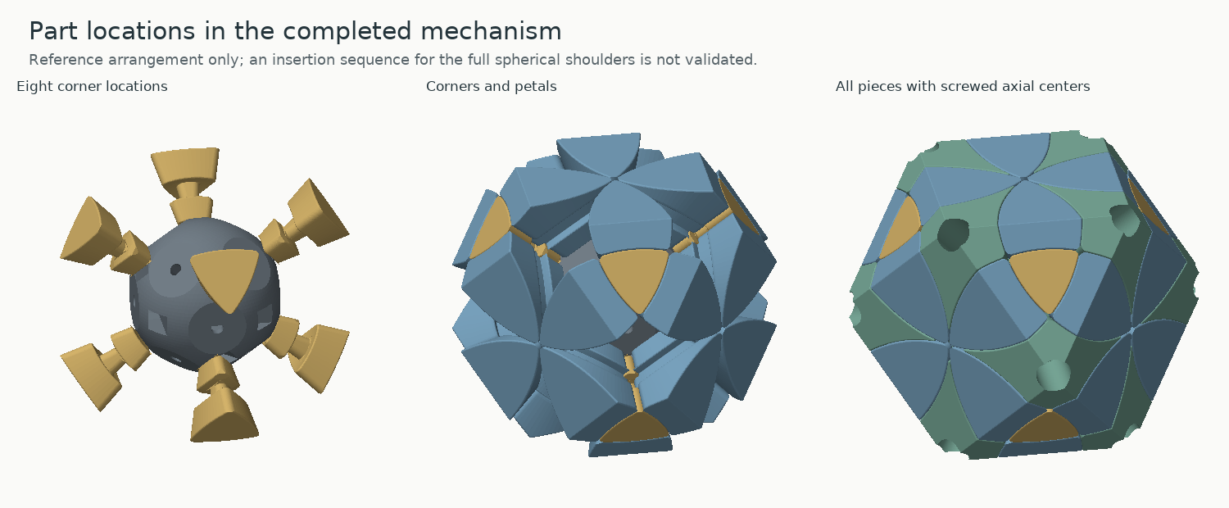
designs/curvy-copter-cuboctahedron-v3.2/images/assembly.png
