lukacslacko/wonkycube/designs/curvy-copter-cuboctahedron-v3.2/images/retention-test-patch.png

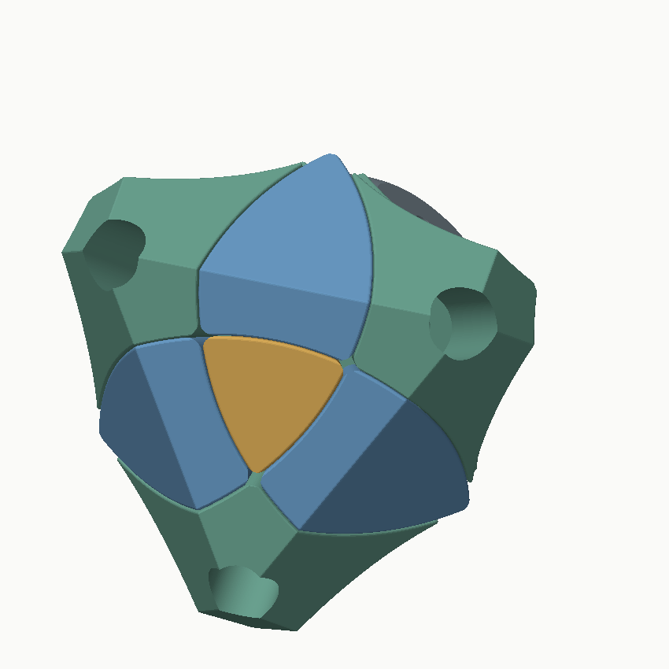
designs/curvy-copter-cuboctahedron-v3.2/images/retention-test-patch.png
